vlgutv22/claude_mate/assets/photos/IMG_4897.jpg

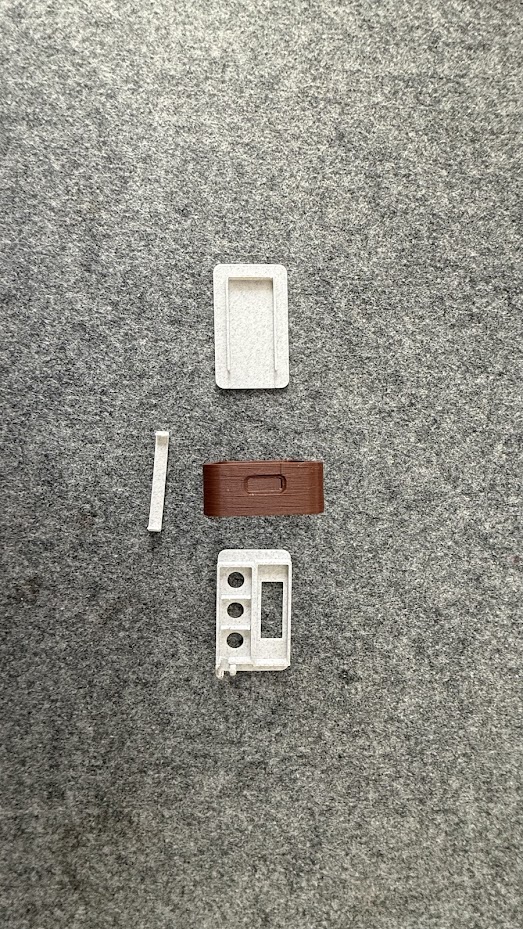
assets/photos/IMG_4897.jpg
