vlgutv22/claude_mate/assets/photos/IMG_4898.jpg

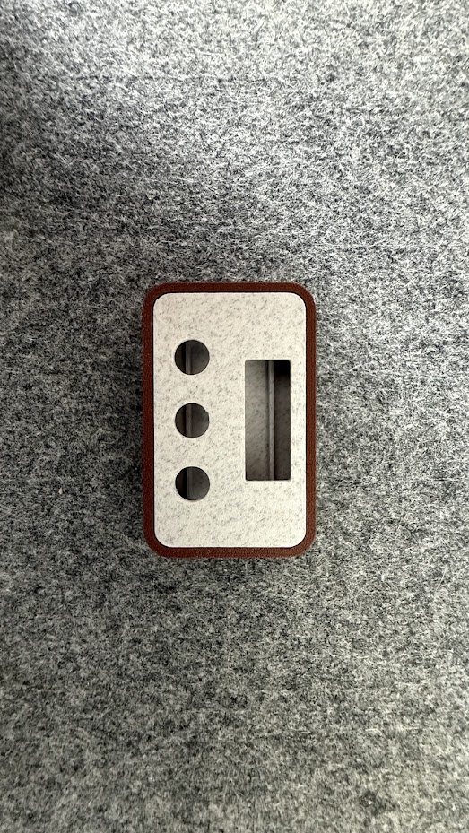
assets/photos/IMG_4898.jpg
