vlgutv22/claude_mate/assets/photos/IMG_4899.jpg

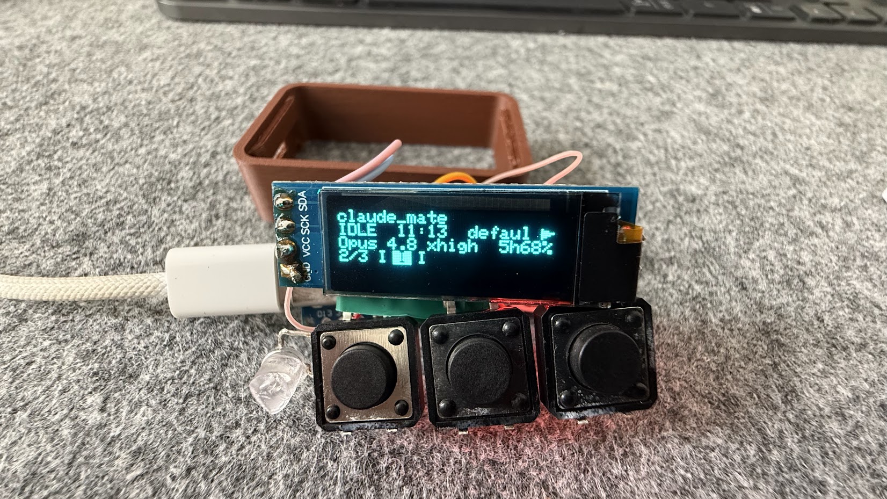
assets/photos/IMG_4899.jpg
