vlgutv22/claude_mate/assets/photos/IMG_4901.jpg

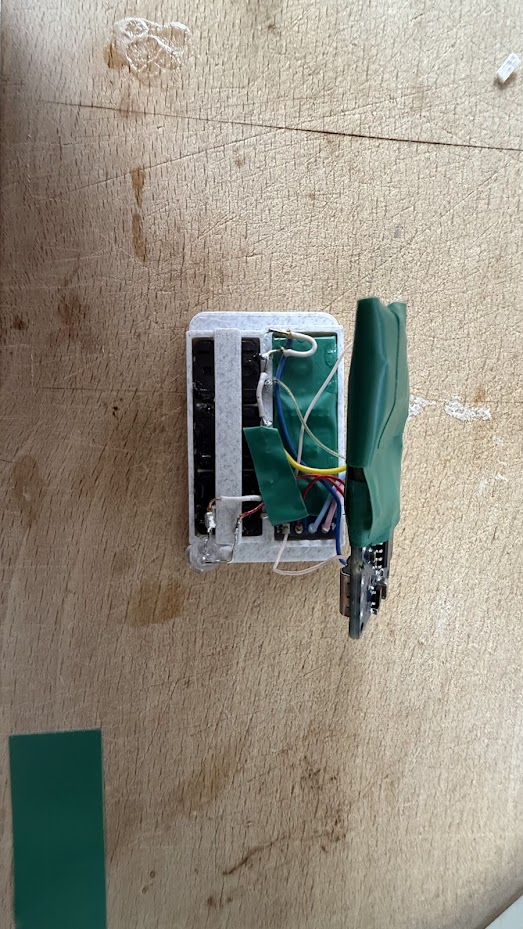
assets/photos/IMG_4901.jpg
