vlgutv22/claude_mate/assets/photos/IMG_4902.jpg

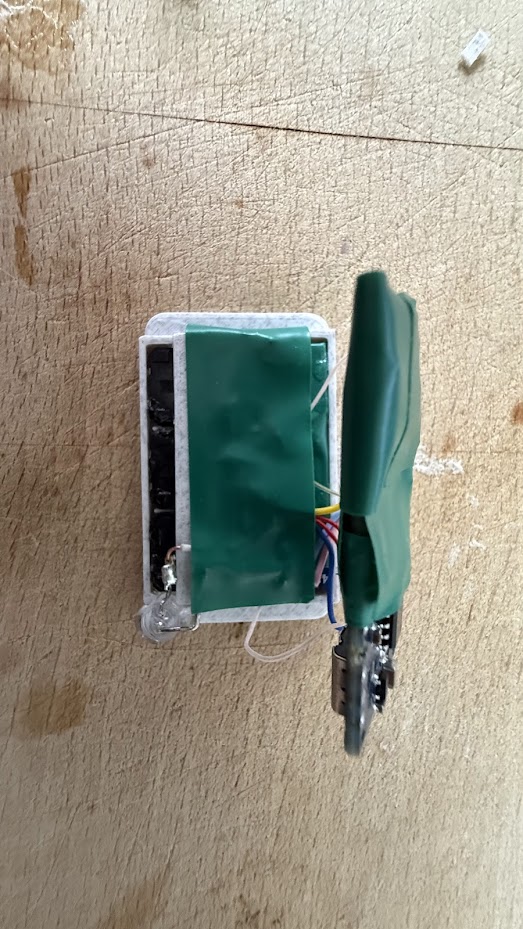
assets/photos/IMG_4902.jpg
