vlgutv22/claude_mate/assets/photos/IMG_4903.jpg

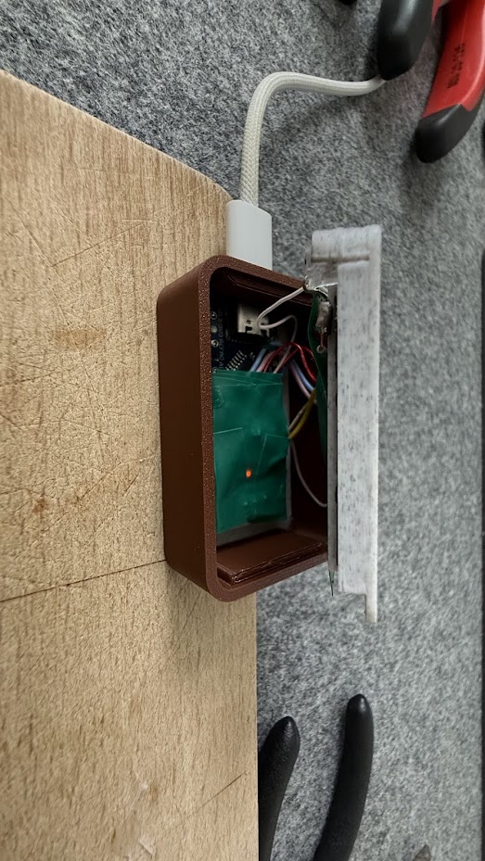
assets/photos/IMG_4903.jpg
