vlgutv22/claude_mate/assets/photos/IMG_4904.jpg

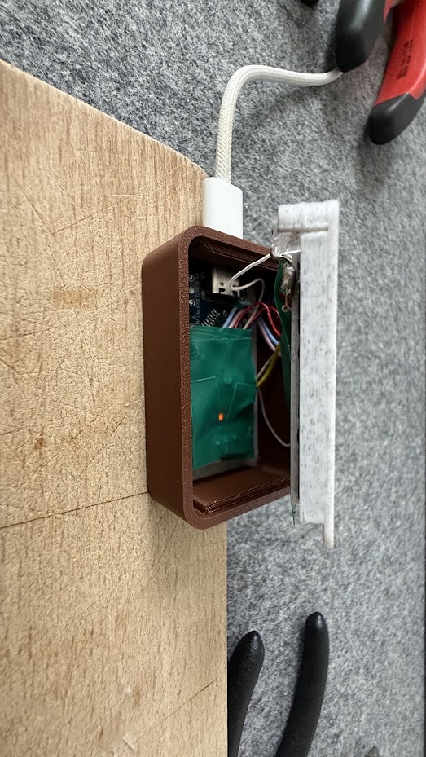
assets/photos/IMG_4904.jpg
