vlgutv22/claude_mate/assets/photos/IMG_4906.jpg

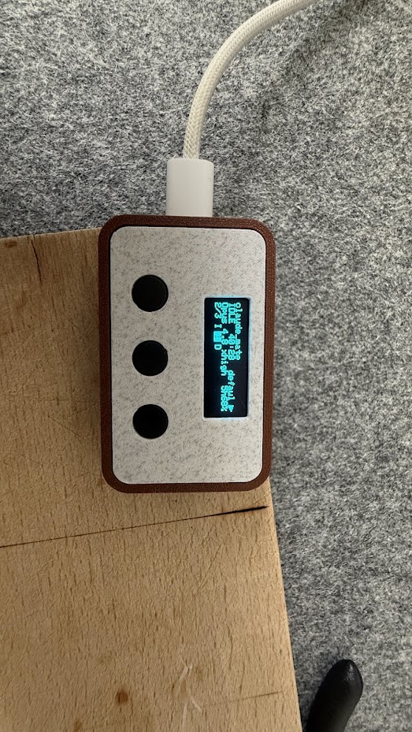
assets/photos/IMG_4906.jpg
