vlgutv22/claude_mate/assets/photos/IMG_4908.jpg

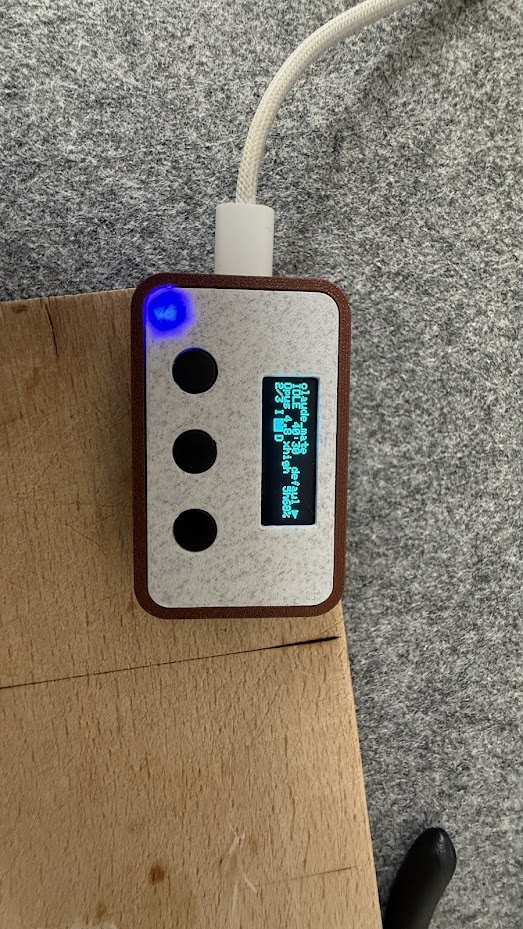
assets/photos/IMG_4908.jpg
