vlgutv22/claude_mate/assets/photos/IMG_4912.jpg

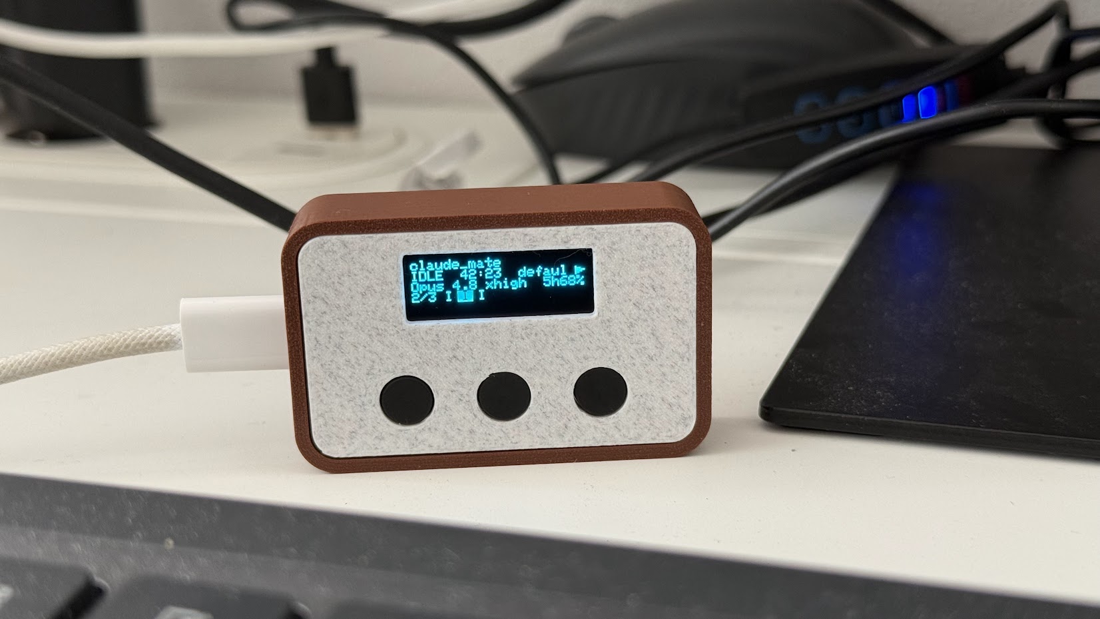
assets/photos/IMG_4912.jpg
