vlgutv22/claude_mate/daemon/claude_mate_daemon.py

#!/usr/bin/env python3
"""
Claude Mate daemon
==================

The "brain" of the Claude Mate USB hardware companion. It:

  1. Listens on a Unix-domain socket (CLAUDE_MATE_SOCK) for status lines emitted
     by Claude Code hooks / the PTY wrapper: "<state>|<session_id>|<name>[|...]".
  2. Manages the device link(s). By default that is a single, continuously-open
     USB serial connection to the Arduino Nano: it auto-detects the port
     (/dev/cu.usbserial* then /dev/cu.usbmodem*), opens it once, keeps it open,
     and auto-reconnects if it disappears. With --tcp it ALSO serves the exact
     same line protocol over TCP, so a wireless companion (the ESP32-S3 build)
     can drive the fleet from across the room. Frames fan out to every connected
     device; button events from any of them are merged into one stream, so a USB
     Nano and a WiFi device can be used side by side.
  3. Keeps ONE urgency-sorted triage queue of sessions
     (error > waiting > done > working > idle; unacknowledged before
     acknowledged inside a class; oldest event first) and renders ONE screen --
     the selected session (normally the queue head, i.e. the thing that needs
     the human most) as a pre-composed 4-row (all size-1) text frame:

         F|<flags>|<sel>|<name>|<state+time · account>|<model+effort · limit>
          |<pos + fleet letters>

     (account = which login the session runs as, limit = its remaining-limit
     chip, both right-aligned; empty for hook-driven sessions.) The firmware
     is a dumb renderer; ALL layout/ordering/selection lives here.
  4. Reads button events from the Arduino on a background thread. The buttons
     mean the same thing at all times (no modes):
        H     -> handshake; the daemon resends the full current state.
        B|P   -> PREV: selection one step up the queue (auto-repeats on hold).
        B|N   -> NEXT: selection one step down the queue (auto-repeats on hold).
        B|G   -> GO (short press): RAISE the terminal of the session SHOWN on
                 the glass (WYSIWYG -- always the name the user is looking at).
                 Raise/activate ONLY; the daemon never collapses, resizes, or
                 miniaturizes any window. An alert is acknowledged as it is
                 raised.
        B|K   -> GO (long press): acknowledge the shown session's alert WITHOUT
                 touching any window.
     A GO/ACK never auto-switches tabs -- it stays on the session it acted on.
     Double-clicking GO toggles FOLLOW mode: PREV/NEXT then also raise the
     selected terminal (raise only, after the selection settles).
  5. Drives the indication LED via V|<KIND>: the pattern for the WORST
     unacknowledged alert class, looping until acknowledged (V|OFF).

Screen ownership rule: the display NEVER changes subject on its own -- only
PREV/NEXT/GO move it. Alerts on other tabs signal through the LED and their
blinking fleet letters; the view stays where the user left it. A GO/ACK acts
on EXACTLY the session whose frame is on the glass -- never a freshly
recomputed head -- so a press can only ever raise the terminal the user is
actually looking at.

Only third-party dependency: pyserial.

Run:
    python3 daemon/claude_mate_daemon.py            # real hardware + hooks
    python3 daemon/claude_mate_daemon.py --mock     # demo with fake sessions

Config via environment variables:
    CLAUDE_MATE_PORT   serial device (default: autodetect)
    CLAUDE_MATE_SOCK   socket path   (default: /tmp/claude-mate.sock)
    CLAUDE_MATE_BAUD   serial baud   (default: 115200)
    CLAUDE_MATE_TCP    set to 1 to also serve the protocol over TCP
    CLAUDE_MATE_TCP_PORT / _TCP_BIND   listener port / bind address
    CLAUDE_MATE_TOKEN / _TOKEN_FILE    shared secret for TCP devices (required
                       for --tcp; the token itself never crosses the wire, see
                       the NetLink handshake)
"""

from __future__ import annotations

import argparse
import glob
import hmac
import json
import os
import queue
import secrets
import signal
import socket
import struct
import subprocess
import sys
import threading
import time
import traceback
import urllib.parse
import wave
from dataclasses import dataclass, field
from typing import Any, Callable, Dict, List, Optional, Tuple, Union

# --------------------------------------------------------------------------- #
# Crash-loop damage control -- BEFORE the first import that can fail
# --------------------------------------------------------------------------- #
# THIS RUNS FIRST ON PURPOSE. launchd opens our stderr (StandardErrorPath) and
# restarts us forever (KeepAlive), so a daemon that dies during import writes
# the same traceback every ThrottleInterval seconds with nothing to stop it. One
# machine reached 1786 restarts and a 50 MB log that way. A cap placed after the
# imports would never have run: the crash was `import serial` itself.
#
# TRUNCATE, DO NOT RENAME. launchd holds the fd, so renaming the file just means
# we keep writing to the same inode under its new name and the visible log stays
# empty forever. ftruncate on the fd we were handed is the only thing that works,
# and with O_APPEND the next write restarts at zero.
LOG_MAX_BYTES = int(os.environ.get("CLAUDE_MATE_LOG_MAX", 8 * 1024 * 1024))


def _cap_crash_log() -> None:
    """Keep a crash loop from eating the disk. Best effort, never fatal."""
    if LOG_MAX_BYTES <= 0:                      # opt out with CLAUDE_MATE_LOG_MAX=0
        return
    try:
        import stat
        st = os.fstat(2)
        if not stat.S_ISREG(st.st_mode) or st.st_size <= LOG_MAX_BYTES:
            return
        os.ftruncate(2, 0)
        os.lseek(2, 0, os.SEEK_SET)
        sys.stderr.write(
            f"[claude-mate] log passed {LOG_MAX_BYTES} bytes and was truncated. "
            f"If this keeps happening the daemon is crash-looping -- the error "
            f"is whatever follows this line.\n"
        )
    except Exception:                           # a pipe, a closed fd, a tty: fine
        pass


_cap_crash_log()

try:
    import serial  # pyserial
except ImportError:  # pragma: no cover - friendly error if dependency missing
    # NAME THE INTERPRETER. The failure this message used to produce was
    # "pyserial is not installed" on a machine where pyserial *was* installed --
    # in the site-packages of the Python the LaunchAgent no longer runs, because
    # /usr/local/bin/python3 is a floating symlink that a python.org update
    # repointed at a fresh version. Without sys.executable in the message there
    # is nothing to tell those two situations apart.
    sys.stderr.write(
        "[claude-mate] ERROR: pyserial is not installed for this interpreter.\n"
        f"[claude-mate]   interpreter: {sys.executable}\n"
        f"[claude-mate]   fix:         {sys.executable} -m pip install -r "
        "daemon/requirements.txt\n"
        "[claude-mate] If you installed it before and it worked, a Python "
        "upgrade probably\n"
        "[claude-mate] moved the interpreter out from under the LaunchAgent. "
        "Re-run install/install.sh,\n"
        "[claude-mate] which pins the daemon to a virtualenv it owns.\n"
    )
    raise

# --------------------------------------------------------------------------- #
# Configuration / constants
# --------------------------------------------------------------------------- #

# Primary FOCUS deep link (hook-driven VS Code sessions). See focus_session().
FOCUS_URI_TEMPLATE = "vscode://anthropic.claude-code/open?session={session_id}"

# Default config (overridable via environment).
DEFAULT_SOCK = "/tmp/claude-mate.sock"
DEFAULT_BAUD = 115200

# Serial port autodetect order (globs).
PORT_GLOBS = ("/dev/cu.usbserial*", "/dev/cu.usbmodem*")

# --- Wireless (TCP) transport ---------------------------------------------- #
# Opt-in (--tcp / CLAUDE_MATE_TCP=1). The device dials US: the daemon's address
# is stable, a DHCP device's is not.
DEFAULT_TCP_PORT = 8787
DEFAULT_TCP_BIND = "0.0.0.0"    # a remote device needs a routable address; the
                                # listener is token-gated (see NetLink)
DEFAULT_TOKEN_FILE = "~/.config/claude-mate/token"
NET_AUTH_TIMEOUT_S = 5.0    # a client must finish the handshake this fast
NET_MAX_LINE = 512          # drop over-long lines (the longest real one is ~94B)
NET_MAX_CLIENTS = 4         # bound the fan-out (a Nano + a few wireless devices)
# ...and bound the peers that have NOT authenticated yet, which is the number an
# attacker controls. Generous next to one real device, trivial next to the
# thousands a laptop can open, and every slot is released within
# NET_AUTH_TIMEOUT_S whatever the peer does or does not send.
NET_MAX_PENDING = 8
MDNS_SERVICE = "_claudemate._tcp"   # advertised via macOS dns-sd so the device
# --- Which networks the listener is allowed to exist on -------------------- #
# THE LISTENER USED TO BE UNCONDITIONAL, and its own docstring explained why
# that was only ever half a design: "the payload itself is plaintext... use it
# on a network you trust". It said nothing about what happens when you carry the
# Mac somewhere else, and the answer was that port 8787 opened itself to a cafe
# exactly as readily as to your living room, and dns-sd announced it to everyone
# on the segment while it did.
#
# A NETWORK IS IDENTIFIED BY ITS GATEWAY'S MAC ADDRESS. Not by SSID: modern
# macOS redacts the SSID and BSSID from every API a daemon can reach without
# Location Services permission, which a LaunchAgent cannot raise a prompt for.
# Not by subnet either -- half the cafes in the world are 192.168.1.0/24, and so
# is half of everyone's house. The gateway's MAC is available from the routing
# table plus the ARP cache, needs no permission, no sudo and no dependency, and
# it actually distinguishes your router from a stranger's.
#
# BE HONEST ABOUT WHAT THIS IS. It is a strong practical control and NOT a
# cryptographic one: someone already on your LAN who knows your home gateway's
# MAC could forge it. It stops the daemon from offering itself to networks you
# have never seen; it does not turn a hostile LAN into a safe one. The plaintext
# threat model above still applies on any network you do trust.
TRUSTED_FILE = "~/.config/claude-mate/trusted-networks"
NET_GATE_POLL_S = 20.0      # how often to re-check which network we are on

MDNS_NAME = "Claude Mate"           # finds the daemon with zero configuration

# Timings (seconds).
DOUBLE_CLICK_S = 0.30        # two GO short-presses within this window = a
                             # double-click (toggles FOLLOW mode). A single GO
                             # is deferred this long to disambiguate.
# ---- MIRROR (the device's terminal view) ---------------------------------- #
# The colour screen fits 53x21 characters at size 1; the status bar takes the
# top band, leaving MIRROR_ROWS for content. Claude's TUI is 80-120 columns
# wide, so rows are CLIPPED, not reflowed -- wrapping a TUI whose box drawing
# and alignment carry meaning turns it into noise, and a clipped-but-truthful
# view is easier to read than a rewrapped one.
MIRROR_COLS = 52
MIRROR_ROWS = 17
MIRROR_POLL_S = 1.0          # refresh cadence while the view is open; polling
                             # stops entirely when it is closed, so an unwatched
                             # fleet costs nothing

FOLLOW_SETTLE_S = 0.25       # in FOLLOW mode, PREV/NEXT raise the selected
                             # terminal only after the selection settles this
                             # long -- so holding to scroll doesn't raise every
                             # window it passes over (raise ONLY, never collapse)
REALERT_SUPPRESS_S = 5.0     # a session re-entering the SAME alert class this
                             # soon after being acknowledged stays acknowledged
                             # (absorbs detection flaps re-firing the LED)
WRAPPER_LIVE_TIMEOUT_S = 1.0  # a live wrapper acks receipt ('go') within ms; a
                              # wedged one (stopped process: the kernel accepts
                              # the connect into the backlog and buffers the
                              # send) costs only this per focus, not the
                              # full completion deadline
WRAPPER_ACK_TIMEOUT_S = 12.0  # overall deadline for the completion ack ('ok');
                              # must exceed the wrapper's worst-case focus op
                              # (~10s: tmux select-window/pane + osascript).
                              # Pre-ack wrappers close the socket at once (EOF),
                              # so the wait degrades to fire-and-forget.
NOTICE_S = 4.0              # how long a transient message holds the middle two
                            # rows. Long enough to read at arm's length after
                            # looking down at the press, short enough that the
                            # screen is never lying about a session for long.
PING_PERIOD = 15.0          # keepalive ping interval
RECONNECT_DELAY = 2.0       # wait between serial (re)connection attempts
SESSION_DONE_TTL = 120.0    # drop a 'done' session after this long with no update
SESSION_IDLE_TTL = 600.0    # drop any stale session after this long

# Screen text geometry (must match the firmware's fixed 4-row layout, all
# size-1: r0 name / r1 state+time / r2 model+effort / r3 position + fleet).
ROW_CHARS = 21              # size-1 rows are 21 chars wide (128 / 6px)

# 4-char state tag shown on the state row.
STATE_TAG = {"working": "WORK", "waiting": "WAIT", "error": "ERR",
             "done": "DONE", "idle": "IDLE"}

# One LETTER per session in the fleet strip (queue order), '|'-separated:
#   I idle  E error  W working (WIP)  D done  B waiting (blocked, needs input)
STATE_LETTER = {"error": "E", "waiting": "B", "working": "W",
                "done": "D", "idle": "I"}

# Triage priority, most urgent first. The queue sorts by
# (class rank, acknowledged?, event time): a fresh error outranks everything,
# unacknowledged before acknowledged inside a class, oldest first (FIFO triage).
STATE_ORDER = {"error": 0, "waiting": 1, "done": 2, "working": 3, "idle": 4}

VALID_STATES = set(STATE_ORDER.keys())

# Alert states nag the human until acknowledged (GO/ACK) or the state changes.
ALERT_STATES = {"error", "waiting", "done"}

# One-shot LED kind on a fresh transition INTO each alert state.
ALERT_KIND = {"error": "ERROR", "waiting": "INPUT", "done": "DONE"}

# Every "until acknowledged" alert plays as a CONTINUOUS firmware LED loop with
# its own distinct rhythm. The firmware repeats the pattern until V|OFF (sent
# when the last unacknowledged member of the class is acknowledged/cleared).
LOOP_KIND = {"error": "ERROR", "waiting": "INPUT", "done": "DONE"}

# ---- Alert sounds (macOS, opt-in) ------------------------------------------ #
# The device itself cannot make a sound: the ESP32-S3 has no DAC, and the
# Waveshare board's 3.3 V rail is a linear LDO with the backlight on a plain
# resistor-limited MOSFET -- there is no switching node whose current the
# firmware could modulate into anything audible. So until a piezo is soldered
# on, the Mac is the only speaker in the system.
#
# That is not purely a workaround. When you are AT the Mac it is the better
# channel: real speakers, distinguishable sounds, and it follows the system
# volume. It stops being enough exactly when the device is across the room on
# battery -- which is the case the piezo will eventually cover.
#
# Off by default. An audible alert on every state change is far more intrusive
# than a colour change, and that has to be opted into rather than inherited.
SOUND_DIR = "/System/Library/Sounds"
ALERT_SOUNDS = {
    "ERROR": "Basso.aiff",     # descending, unmistakably "something went wrong"
    "INPUT": "Glass.aiff",     # bright and short: a question, not a failure
    "DONE":  "Hero.aiff",      # rising, resolved
    "START": "Pop.aiff",       # a tick; only fires when nothing else is pending
}
SOUND_MIN_GAP_S = 2.0          # floor between sounds, whatever the state does

# SHIP IT, the game on the device, over `O|SFX|<code>`. The board has no DAC, no
# speaker and a backlight circuit with no inductor to abuse, so if the game is to
# make a noise at all it has to be this machine making it.
#
# These were macOS system alert sounds for one version, and that was wrong in a
# way that only shows up when you play: Basso and Glass are the vocabulary of an
# OS telling you something, not of a game. The browser prototype uses WebAudio
# square and sawtooth oscillators, and THAT is the sound the device should make
# -- so the recipes below are the prototype's literals, and the daemon renders
# them to WAV once at startup rather than reaching for a file someone at Apple
# designed for a different purpose.
#
#   (frequencies Hz), note seconds, waveform, peak gain
#
# A recipe of several frequencies is played as a SEQUENCE, one note per entry,
# each `dur` long -- that is what makes the merge an arpeggio and the ship a
# fanfare rather than a chord.
SFX_RECIPES = {
    "J": ((520, 760),                  0.055, "square",   0.050),  # jump
    "S": ((300, 150),                  0.050, "square",   0.050),  # stomped a bug
    "M": ((660, 880, 1320),            0.065, "square",   0.055),  # merged a PR
    "H": ((180, 120),                  0.090, "sawtooth", 0.050),  # a bug got you
    "R": ((180, 120),                  0.090, "sawtooth", 0.050),  # re-scoped
    "F": ((400, 260, 160),             0.060, "sawtooth", 0.050),  # fell
    "X": ((400, 260, 160),             0.060, "sawtooth", 0.050),  # slipped
    "W": ((523, 659, 784, 1047, 1319), 0.110, "square",   0.060),  # shipped
}
# R and X are not distinct sounds, and that is the prototype's choice rather
# than an oversight here: a priority change reads as a hit and a slipped
# milestone reads as a fall, which is what they are.

# The prototype's gains are WebAudio linear gain into a browser, and the same
# numbers rendered to a file and pushed through afplay land far below the system
# alerts they sit beside -- quiet enough to miss over a fan. Everything is scaled
# by this one factor, so the sounds keep their RELATIVE levels (the ship fanfare
# stays the loudest) while landing somewhere a person can hear.
SFX_GAIN     = 5.0
SFX_RATE     = 44100
SFX_ATTACK_S = 0.008           # the prototype's linear attack, then exp decay
SFX_FLOOR    = 0.0008          # ...to here, which is where its ramp ends

# Rendered WAVs live here. The version in the name is load-bearing: change a
# recipe without changing it and every machine keeps playing the old sound from
# cache forever.
SFX_CACHE_DIR = os.path.join(
    os.path.expanduser("~/Library/Caches/claude-mate"), "sfx-v1")

GAME_SOUND_MIN_GAP_S = 0.06

# A device with no token redials every couple of seconds; say what to do about
# it at most this often, or the advice buries itself.
NO_TOKEN_LOG_GAP_S = 60.0

# Sentinel for "we have not told the firmware a loop state yet", so the first
# resolve always emits (V|OFF) and clears any stale loop left by a prior daemon.
_LOOP_UNSET = "\x00unset"


def _sfx_render(freqs, dur: float, wave: str, vol: float) -> bytes:
    """One recipe -> 16-bit mono PCM, reproducing WebAudio's envelope exactly.

    The prototype gives each note its own oscillator and gain node, ramps the
    gain linearly 0 -> vol over 8 ms, then EXPONENTIALLY down to 0.0008 by the
    note's end. The exponential matters: a linear fade of a square wave at these
    durations sounds like a click with a tail, and the whole character of the
    thing is in that decay curve. WebAudio's exponentialRampToValueAtTime is
    v0 * (v1/v0)^(progress), which is what the pow() below is.

    Naive (non-band-limited) square and sawtooth, deliberately. WebAudio uses
    band-limited wavetables, so this aliases slightly where that does not -- at
    these frequencies the difference is inaudible, and the alternative is a
    Fourier synthesis nobody can check against the prototype by ear."""
    frames = bytearray()
    span   = max(dur - SFX_ATTACK_S, 1e-6)
    ratio  = SFX_FLOOR / vol
    peak   = min(vol * SFX_GAIN, 0.85)         # headroom against clipping
    for f in freqs:
        n = int(SFX_RATE * dur)
        for i in range(n):
            t = i / SFX_RATE
            if t < SFX_ATTACK_S:
                env = t / SFX_ATTACK_S
            else:
                env = pow(ratio, (t - SFX_ATTACK_S) / span)
            # Phase restarts per note, as it must: the prototype creates a new
            # oscillator for each one.
            ph = (f * t) % 1.0
            sample = (2.0 * ph - 1.0) if wave == "sawtooth" else (1.0 if ph < 0.5 else -1.0)
            v = int(max(-1.0, min(1.0, peak * env * sample)) * 32767)
            frames += struct.pack("<h", v)
    return bytes(frames)


def sfx_build_cache() -> dict:
    """Render every recipe to a WAV once and return {code: path}.

    Returns {} on any failure -- a game with no sound is a working game, and a
    daemon that will not start because it could not write a beep is not."""
    out = {}
    try:
        os.makedirs(SFX_CACHE_DIR, exist_ok=True)
        for code, (freqs, dur, wave_t, vol) in SFX_RECIPES.items():
            path = os.path.join(SFX_CACHE_DIR, f"{code}.wav")
            if not os.path.exists(path):
                pcm = _sfx_render(freqs, dur, wave_t, vol)
                # Written to a temp name and renamed, so a daemon killed
                # mid-render cannot leave a truncated WAV cached forever.
                tmp = path + ".part"
                with wave.open(tmp, "wb") as w:
                    w.setnchannels(1)
                    w.setsampwidth(2)
                    w.setframerate(SFX_RATE)
                    w.writeframes(pcm)
                os.replace(tmp, path)
            out[code] = path
    except Exception as exc:
        log(f"game sound: could not build the cache ({exc}); game is silent")
        return {}
    return out


def log(msg: str) -> None:
    """Clean, timestamped logging to stderr."""
    ts = time.strftime("%H:%M:%S")
    sys.stderr.write(f"[claude-mate {ts}] {msg}\n")
    sys.stderr.flush()


# --------------------------------------------------------------------------- #
# Session model + thread-safe registry
# --------------------------------------------------------------------------- #


@dataclass
class Session:
    """One Claude Code session tracked by the daemon."""
    key: str                       # registry key (session_id or name)
    name: str                      # cwd basename, display name
    state: str = "idle"            # working | waiting | error | done | idle
    sid: str = ""                  # session_id (may be empty)
    cwd: str = ""                  # working directory, if known
    last_update_ts: float = field(default_factory=time.time)
    state_since: float = field(default_factory=time.time)  # when current state began
    model: str = ""                # model in use, e.g. "Opus 4.8" (PTY wrapper)
    effort: str = ""               # effort level, e.g. "xhigh" (PTY wrapper)
    account: str = ""              # account the session runs as, e.g. "work" (PTY wrapper)
    limit: str = ""                # remaining-limit chip, e.g. "5h82%" (PTY wrapper)
    focus_ctrl: str = ""           # PTY-wrapper control socket for FOCUS (if any)
    acked: bool = True             # alert (done/waiting/error) seen by the human?
    last_ack_state: str = ""       # alert class most recently acknowledged...
    last_ack_ts: float = 0.0       # ...and when (re-alert flap suppression)

    def display_seconds(self) -> float:
        """The time shown on the info row: time in the current state.

        For 'working' that IS the live turn runtime; for an alert state it is
        the triage-critical number -- how long this has been waiting on the
        human; for 'idle' how long it has been sitting there.
        """
        return max(0.0, time.time() - self.state_since)

    def unacked_alert(self) -> bool:
        return self.state in ALERT_STATES and not self.acked


class Registry:
    """Thread-safe collection of sessions keyed by session_id (or name)."""

    def __init__(self) -> None:
        self._lock = threading.Lock()
        self._sessions: Dict[str, Session] = {}

    def update(self, state: str, sid: str, name: str, cwd: str = "",
               focus_ctrl: str = "", model: str = "",
               effort: str = "", account: str = "",
               limit: str = "") -> Optional[str]:
        """Apply a status update from a hook, the PTY wrapper, or the mock injector.

        Returns the one-shot LED KIND for this session's own transition
        (START/DONE/INPUT/ERROR), or None for a keepalive / silent change.

        Models "finished but not yet acknowledged": a turn ending (working ->
        idle) becomes 'done' and STAYS 'done' (alerting) until the user
        acknowledges it; later idle keepalives must not clear it.
        """
        if state not in VALID_STATES:
            log(f"ignoring update with invalid state: {state!r}")
            return None
        key = sid if sid else (name if name else "unknown")
        now = time.time()
        with self._lock:
            sess = self._sessions.get(key)
            if sess is None:
                sess = Session(key=key, name=name or key)
                self._sessions[key] = sess
            # Update fields.
            if name:
                sess.name = name
            if sid:
                sess.sid = sid
            if cwd:
                sess.cwd = cwd
            if focus_ctrl:
                sess.focus_ctrl = focus_ctrl
            if model:
                sess.model = model
            if effort:
                sess.effort = effort
            if account:
                sess.account = account
            if limit:
                sess.limit = limit
            prev_state = sess.state
            sess.last_update_ts = now

            # Resolve the EFFECTIVE state under the done-until-acknowledged model.
            eff = state
            if state == "idle":
                if prev_state == "working":
                    eff = "done"                 # just finished -> needs ack
                elif prev_state == "done" and not sess.acked:
                    eff = "done"                 # keepalive while unacknowledged

            changed = (eff != prev_state)
            if changed:
                sess.state_since = now           # live "time in state" anchor
            sess.state = eff

            # Acknowledgment + one-shot LED kind on a real transition.
            haptic: Optional[str] = None
            if changed:
                if eff in ALERT_STATES:          # done/waiting/error: fresh alert
                    # Flap suppression: re-entering the SAME alert class right
                    # after the human acknowledged it stays acknowledged, so a
                    # bouncing detector can't re-fire the LED he just silenced.
                    if (sess.last_ack_state == eff
                            and (now - sess.last_ack_ts) < REALERT_SUPPRESS_S):
                        sess.acked = True
                    else:
                        sess.acked = False       # nag until acknowledged
                        haptic = ALERT_KIND[eff]
                elif eff == "working":
                    sess.acked = True
                    sess.last_ack_state = ""     # real forward progress: a
                    sess.last_ack_ts = 0.0       # future alert is NEW, not a flap
                    haptic = "START"             # job (re)started: calm tick
                else:                            # idle
                    sess.acked = True
            return haptic

    def remove(self, key: str) -> None:
        with self._lock:
            self._sessions.pop(key, None)

    def acknowledge(self, sess: Optional["Session"]) -> None:
        """GO/ACK pressed: mark this session's alert as seen. A finished (done)
        session becomes idle; a waiting/error session is silenced but keeps its
        state (it still shows, just stops nagging) until it changes on its own."""
        if sess is None:
            return
        with self._lock:
            if sess.state in ALERT_STATES:
                sess.last_ack_state = sess.state
                sess.last_ack_ts = time.time()
            sess.acked = True
            if sess.state == "done":
                sess.state = "idle"
                sess.state_since = time.time()

    def top_alert(self) -> Optional["Session"]:
        """The most urgent unacknowledged session needing the human (error >
        waiting > done, oldest first), or None. Drives the LED loop class.
        Sorted by URGENCY independently of the display order (which is a
        stable alphabetical order, see queue())."""
        with self._lock:
            items = [s for s in self._sessions.values() if s.unacked_alert()]
        items.sort(key=lambda s: (STATE_ORDER.get(s.state, 99), s.state_since))
        return items[0] if items else None

    def prune(self) -> None:
        """Drop stale/finished sessions so the queue stays tidy."""
        now = time.time()
        with self._lock:
            dead: List[str] = []
            for key, s in self._sessions.items():
                age = now - s.last_update_ts
                if s.state == "idle" and age > SESSION_IDLE_TTL:
                    dead.append(key)
                elif s.state == "done" and age > SESSION_DONE_TTL:
                    dead.append(key)
                elif age > SESSION_IDLE_TTL:
                    dead.append(key)
            for key in dead:
                self._sessions.pop(key, None)
            if dead:
                log(f"pruned {len(dead)} stale session(s)")

    def queue(self) -> List[Session]:
        """The display/navigation order: STABLE, alphabetical by name (then key
        as a deterministic tiebreak). Tabs keep their position as their states
        change -- they never shuffle under the user. Urgency drives the LED
        separately (see top_alert()), not this order."""
        with self._lock:
            items = list(self._sessions.values())
        items.sort(key=lambda s: (s.name.lower(), s.key))
        return items

    def count(self) -> int:
        with self._lock:
            return len(self._sessions)


# --------------------------------------------------------------------------- #
# Serial link: open once, keep open, auto-reconnect.
# --------------------------------------------------------------------------- #


class SerialLink:
    """Owns the single serial connection and serializes writes."""

    def __init__(self, port: Optional[str], baud: int) -> None:
        self._configured_port = port  # None => autodetect
        self._baud = baud
        self._ser: Optional[serial.Serial] = None
        self._lock = threading.Lock()  # guards writes + (re)connect
        self._provision_token: Optional[str] = None
        self._pending_provision = False   # armed on open, spent on the first K/H

    def set_provision_token(self, token: Optional[str]) -> None:
        """The secret to hand a device that arrives on the cable. See _provision().

        Set only when a wireless transport is up, because that is the only time
        there is a shared secret to share -- a USB-only daemon has nothing to
        provision the device FOR.
        """
        self._provision_token = token

    @staticmethod
    def autodetect() -> Optional[str]:
        """Find a likely Arduino device by glob priority."""
        for pattern in PORT_GLOBS:
            matches = sorted(glob.glob(pattern))
            if matches:
                return matches[0]
        return None

    def _resolve_port(self) -> Optional[str]:
        if self._configured_port:
            return self._configured_port if os.path.exists(self._configured_port) else None
        return self.autodetect()

    def is_open(self) -> bool:
        return self._ser is not None and self._ser.is_open

    # Same names LinkHub exposes, so the maintainer can drive either link type
    # without caring which transport it got.
    def serial_is_open(self) -> bool:
        return self.is_open()

    def ensure_serial_open(self) -> bool:
        return self.ensure_open()

    def ensure_open(self) -> bool:
        """Try to (re)open the port. Returns True if open afterwards."""
        with self._lock:
            if self.is_open():
                return True
            port = self._resolve_port()
            if not port:
                return False
            try:
                self._ser = serial.Serial(
                    port=port,
                    baudrate=self._baud,
                    bytesize=serial.EIGHTBITS,
                    parity=serial.PARITY_NONE,
                    stopbits=serial.STOPBITS_ONE,
                    timeout=0.5,        # read timeout
                    write_timeout=2.0,
                )
                log(f"serial opened on {port} @ {self._baud} 8N1")
                # Opening the port resets the Nano (~1.5s); it will emit H when
                # ready, prompting a full state resend. We do not block here.
                #
                # The token is NOT sent yet -- see provision_if_ours(). A `P`
                # asks whoever is on this port to identify itself; a Claude Mate
                # answers `K` (or `H` on boot), and only then does a secret go
                # down the wire.
                self._pending_provision = True
                self._write_locked("P")
                return True
            except (serial.SerialException, OSError) as exc:
                log(f"serial open failed on {port}: {exc}")
                self._close_locked()
                return False

    def provision_if_ours(self) -> None:
        """The device answered the protocol, so it is safe to give it the token.

        Called by the reader when a `K` or `H` arrives. THE HANDSHAKE IS THE
        POINT: autodetect() takes the first match of a glob, and PORT_GLOBS tries
        `/dev/cu.usbserial*` BEFORE the `/dev/cu.usbmodem*` the S3 actually
        enumerates as -- so any FTDI or CH340 dongle on the desk outranked the
        real device and was handed the shared secret, on every reconnect. It
        cannot answer `K`, so it no longer gets one.
        """
        with self._lock:
            if not self._pending_provision:
                return
            self._pending_provision = False
            self._provision_locked()

    def _write_locked(self, line: str) -> None:
        """Write with the lock already held. Failures are the caller's problem."""
        if not self.is_open():
            return
        try:
            self._ser.write((line + "\n").encode("ascii", errors="replace"))
        except (serial.SerialException, OSError):
            pass

    def _provision_locked(self) -> None:
        """Give the device on the cable this daemon's token, once per open.

        THE CABLE IS THE ANSWER TO "how do I connect it after a factory reset",
        and it should not involve the human at all. A wiped board comes up on
        BLE with no token; the daemon connects, gets A|NOTOKEN, and both ends
        then sit there knowing exactly what is wrong and doing nothing about it
        -- while a USB cable, over which provisioning is already the documented
        and trusted path, is plugged into the same two devices.

        Unconditional rather than conditional on "does it need one", because
        there is no way to ask over this link (USB has no handshake -- it is
        trusted by being physical) and because the daemon's token is the
        authority: a device holding a different one is a device that cannot
        link, so overwriting is the repair, not a side effect. NVS skips a write
        whose value is unchanged, so the steady state costs nothing.

        T| is a CONFIG verb, handled before the protocol on the firmware side,
        and the Nano ignores it as an unknown line -- so this is safe to send to
        whatever happens to be on the port.
        """
        token = self._provision_token
        if not token or os.environ.get("CLAUDE_MATE_NO_USB_PROVISION") == "1":
            return
        # THE PORT CAN CLOSE BETWEEN THE ARM AND THE WRITE, and it is not a rare
        # window: the arm is spent by a K/H reaching the ButtonReader, which the
        # hub forwards here from WHATEVER transport it arrived on -- so a device
        # that drops off the cable and says hello over the radio a few seconds
        # later lands exactly here with `self._ser` already None. That is an
        # AttributeError, not a SerialException, so the except below did not
        # catch it and it killed the reader thread. Observed in the wild: a
        # serial read failure at 21:37:42 and a BLE connect at 21:37:48 left the
        # daemon running with every device button dead.
        if not self.is_open():
            return
        try:
            self._ser.write(f"T|{token}\n".encode("ascii", errors="replace"))
        except (serial.SerialException, OSError) as exc:
            # Not fatal and not worth closing the port over: the link still
            # works, it just may not be able to authenticate over the radio.
            log(f"serial: could not hand the device a token: {exc}")
            return
        log("serial: handed the device this daemon's token (USB provisioning)")

    def _close_locked(self) -> None:
        if self._ser is not None:
            try:
                self._ser.close()
            except Exception:
                pass
        self._ser = None
        # The arm belongs to the open that made it. Leaving it set means the
        # next K/H -- possibly from a device that is now on the radio, with no
        # cable at all -- tries to provision a port that is gone; ensure_open()
        # re-arms it if and when the cable comes back.
        self._pending_provision = False

    def close(self) -> None:
        with self._lock:
            self._close_locked()

    def write_line(self, line: str) -> bool:
        """Write one newline-terminated ASCII line. Returns success."""
        data = (line.rstrip("\n") + "\n").encode("ascii", errors="replace")
        with self._lock:
            if not self.is_open():
                return False
            try:
                # No flush(): tcdrain has no timeout bound, and a wedged port
                # would stall every caller holding the Screen lock. write() is
                # bounded by write_timeout and these lines are tiny; the kernel
                # drains them at line rate.
                self._ser.write(data)
                return True
            except (serial.SerialException, OSError) as exc:
                log(f"serial write failed ({line!r}): {exc}")
                self._close_locked()  # mark dead -> reconnect loop will recover
                return False

    def read_line(self) -> Optional[str]:
        """Read one line (blocking up to the read timeout). None on no-data/err."""
        ser = self._ser
        if ser is None or not ser.is_open:
            return None
        try:
            raw = ser.readline()
        except (serial.SerialException, OSError) as exc:
            log(f"serial read failed: {exc}")
            self.close()
            return None
        if not raw:
            return None
        try:
            return raw.decode("ascii", errors="replace").strip()
        except Exception:
            return None


# --------------------------------------------------------------------------- #
# Wireless link: the same line protocol over TCP (opt-in).
# --------------------------------------------------------------------------- #


def load_token(explicit: Optional[str]) -> Optional[str]:
    """Resolve the shared secret: --token/env first, then the token file.

    A file keeps the secret out of the LaunchAgent plist (which is readable by
    every process on the machine); we require it to be non-empty but do not
    enforce permissions, since the user may deliberately share it.
    """
    if explicit:
        return explicit.strip() or None
    path = os.path.expanduser(os.environ.get("CLAUDE_MATE_TOKEN_FILE",
                                             DEFAULT_TOKEN_FILE))
    try:
        with open(path, "r", encoding="utf-8") as fh:
            return fh.read().strip() or None
    except OSError:
        return None


def ensure_token(explicit: Optional[str]) -> Optional[str]:
    """load_token(), but MAKE one rather than refusing if there is none.

    --tcp used to fail closed on a missing token and fall back to USB-only,
    which was the right instinct aimed at the wrong problem. The danger being
    guarded against is an UNAUTHENTICATED listener; a freshly generated 32-byte
    secret is not that. What the old behaviour actually produced was a dead end:
    the device's setup portal asks for a token, and the only way to have one was
    to have already known to create the file by hand. Generating it here closes
    that loop -- run the daemon once, read the token off the terminal, type it
    into the portal.

    Written 0600, and only ever created; an existing file is never rewritten, so
    this cannot silently invalidate a device that is already provisioned.
    """
    tok = load_token(explicit)
    if tok:
        return tok
    if explicit:                       # they passed one and it was blank
        return None
    path = os.path.expanduser(os.environ.get("CLAUDE_MATE_TOKEN_FILE",
                                             DEFAULT_TOKEN_FILE))
    tok = secrets.token_hex(32)
    try:
        os.makedirs(os.path.dirname(path), exist_ok=True)
        # Create-exclusive: if another daemon raced us to it, read theirs rather
        # than clobbering a token a device may already be provisioned with.
        fd = os.open(path, os.O_WRONLY | os.O_CREAT | os.O_EXCL, 0o600)
        with os.fdopen(fd, "w", encoding="utf-8") as fh:
            fh.write(tok + "\n")
    except FileExistsError:
        return load_token(None)
    except OSError as exc:
        log(f"ERROR: could not create a token at {path}: {exc}")
        return None
    log("")
    log("  no shared token existed, so one was generated:")
    log("")
    log(f"      {tok}")
    log("")
    log(f"  saved to {path} (mode 0600).")
    log("  Type it into the device's wifi setup portal, in 'Shared token'.")
    log("")
    return tok


class NetLink:
    """Serves the daemon<->device line protocol to token-authenticated TCP peers.

    The device is the CLIENT: the daemon's address is stable and discoverable
    (mDNS), a DHCP device's is not, and dialling out means the device needs no
    inbound reachability at all.

    HANDSHAKE (the token never crosses the wire, so sniffing one session cannot
    reveal it and a captured handshake cannot be replayed against a later one):

        daemon -> device   C|<nonce>          32 hex chars, fresh per connection
        device -> daemon   A|<mac>            hex HMAC-SHA256(token, nonce)
        daemon -> device   A|OK               ...or A|NO and the socket closes

    After A|OK the socket carries exactly the bytes the serial link would: F|/V|/P
    down, H/K/B| up. The device sends H, which makes the daemon resend full state
    -- the same recovery path a Nano replug uses.

    Writes fan out to every authenticated client and reads from all of them merge
    into one queue, so a USB Nano and a wireless device work side by side. A
    device that vanishes without a FIN (walked out of WiFi range) is reaped the
    first time a frame or ping fails to send.

    THREAT MODEL: the payload itself is plaintext. Anyone who can sniff your LAN
    can read session names, models and states, and an on-path attacker could
    inject button events into an established connection. Use it on a network you
    trust; it is off unless you ask for it.
    """

    def __init__(self, bind: str, port: int, token: str,
                 rx: "queue.Queue[str]") -> None:
        self._bind = bind
        self._port = port
        self._token = token.encode("utf-8")
        self._rx = rx
        self._srv: Optional[socket.socket] = None
        self._lock = threading.Lock()           # guards _clients
        self._clients: List[socket.socket] = []
        self._stop_evt = threading.Event()
        self._threads: List[threading.Thread] = []
        self._pending = 0                       # connections still handshaking
        self._no_token_logged = 0.0             # throttle for _log_no_token

    # ---- lifecycle -------------------------------------------------------- #

    def start(self) -> bool:
        """Bind + listen and start accepting. False if the port is unusable.

        RESTARTABLE, because NetworkGate closes the listener when the Mac moves
        to an untrusted network and opens it again when it comes home. stop()
        sets _stop_evt and nothing used to clear it, so the second start() built
        a listener and handed it to an accept loop whose very first `while not
        self._stop_evt.is_set()` was already false -- a socket bound, listening,
        and attached to nobody, which is worse than a failure because it looks
        exactly like success.
        """
        self._stop_evt.clear()
        # Drop the corpses of previous connections. This list is appended to
        # once per accepted connection and never pruned, so on a long-lived
        # daemon it is an unbounded list of dead Thread objects -- slow-motion
        # memory growth that anyone able to reach the port can drive.
        self._threads = [t for t in self._threads if t.is_alive()]
        try:
            srv = socket.socket(socket.AF_INET, socket.SOCK_STREAM)
            srv.setsockopt(socket.SOL_SOCKET, socket.SO_REUSEADDR, 1)
            srv.bind((self._bind, self._port))
            srv.listen(NET_MAX_CLIENTS)
            srv.settimeout(0.5)                 # so the accept loop can stop
        except OSError as exc:
            log(f"TCP listen failed on {self._bind}:{self._port}: {exc}")
            return False
        self._srv = srv
        t = threading.Thread(target=self._accept_loop, name="net-accept",
                             daemon=True)
        t.start()
        self._threads.append(t)
        log(f"TCP listening on {self._bind}:{self._port} (token required)")
        return True

    def stop(self) -> None:
        self._stop_evt.set()
        if self._srv is not None:
            # SHUTDOWN BEFORE CLOSE, and it is not belt-and-braces. close() on
            # a listening socket does not wake a thread already blocked in
            # accept() on Linux, and the kernel keeps the socket serving until
            # that thread lets go -- so "the listener is closed" was true of our
            # bookkeeping and false of the port for up to one accept timeout.
            # For a control whose whole job is to shut the door when the Mac
            # joins a network you do not trust, "closed in a moment" is not the
            # same promise as "closed". shutdown() wakes the accept immediately;
            # it is meaningless on a listening socket on some platforms, hence
            # the guard rather than a check.
            try:
                self._srv.shutdown(socket.SHUT_RDWR)
            except OSError:
                pass
            try:
                self._srv.close()
            except OSError:
                pass
            self._srv = None
        with self._lock:
            clients, self._clients = self._clients, []
        for c in clients:
            self._shutdown(c)

    @staticmethod
    def _shutdown(sock: socket.socket) -> None:
        try:
            sock.shutdown(socket.SHUT_RDWR)
        except OSError:
            pass
        try:
            sock.close()
        except OSError:
            pass

    # ---- accept + authenticate -------------------------------------------- #

    def _accept_loop(self) -> None:
        while not self._stop_evt.is_set():
            srv = self._srv
            if srv is None:
                return
            try:
                conn, addr = srv.accept()
            except socket.timeout:
                continue
            except OSError:
                return                          # listener closed: we are done
            # THE CAP USED TO COUNT THE WRONG THING. _clients holds peers that
            # have ALREADY authenticated, so a peer that never finishes the
            # handshake was never counted -- and every accept span a thread that
            # lived for the full NET_AUTH_TIMEOUT_S. Anyone who could reach the
            # port could therefore hold an unbounded number of threads open by
            # connecting and saying nothing, without knowing the token at all.
            # Bounding connections IN THE HANDSHAKE is the check that matters;
            # the authenticated cap below stays as the fan-out bound it always
            # was.
            with self._lock:
                too_many = (len(self._clients) >= NET_MAX_CLIENTS
                            or self._pending >= NET_MAX_PENDING)
                if not too_many:
                    self._pending += 1
            if too_many:
                log(f"TCP refused {addr[0]}: {len(self._clients)} linked, "
                    f"{self._pending} in handshake")
                self._shutdown(conn)
                continue
            t = threading.Thread(target=self._serve, args=(conn, addr),
                                 name="net-client", daemon=True)
            t.start()
            with self._lock:
                self._threads = [x for x in self._threads if x.is_alive()]
                self._threads.append(t)

    def _authenticate(self, conn: socket.socket, peer: str) -> bool:
        """Nonce challenge / HMAC response. False = reject (caller closes)."""
        nonce = secrets.token_hex(16)
        expect = hmac.new(self._token, nonce.encode("ascii"),
                          "sha256").hexdigest()
        try:
            # One budget for the entire handshake, wall-clock, from before the
            # challenge goes out. See _read_line_blocking().
            deadline = time.monotonic() + NET_AUTH_TIMEOUT_S
            conn.settimeout(NET_AUTH_TIMEOUT_S)
            conn.sendall(f"C|{nonce}\n".encode("ascii"))
            reply = self._read_line_blocking(conn, deadline=deadline)
        except (OSError, socket.timeout):
            log(f"TCP {peer}: handshake timed out")
            return False
        if reply is None or not reply.startswith("A|"):
            log(f"TCP {peer}: bad handshake {reply!r}")
            return False
        # A device that knows it has no token says so, rather than hanging up and
        # leaving us to report "bad handshake None" -- which reads like a crash
        # or a network fault and sends you looking in the wrong place entirely.
        # It is the commonest wireless failure by far, because it is what a
        # cleared token looks like, so it gets the one message that says exactly
        # what to do about it.
        if reply.strip().upper() == "A|NOTOKEN":
            self._log_no_token(peer)
            try:
                conn.sendall(b"A|NO\n")
            except OSError:
                pass
            return False
        # compare_digest keeps the comparison time independent of how much of
        # the MAC an attacker guessed right.
        if not hmac.compare_digest(reply[2:].strip().lower(), expect):
            log(f"TCP {peer}: token rejected")
            try:
                conn.sendall(b"A|NO\n")
            except OSError:
                pass
            time.sleep(0.5)                     # take the shine off brute force
            return False
        try:
            conn.sendall(b"A|OK\n")
        except OSError:
            return False
        return True

    def _log_no_token(self, peer: str) -> None:
        """The actionable message, throttled.

        The device redials every couple of seconds, so an unthrottled message
        would bury the log in copies of itself -- which is its own kind of
        useless, and exactly what `bad handshake None` was already doing."""
        now = time.time()
        if now - self._no_token_logged < NO_TOKEN_LOG_GAP_S:
            return
        self._no_token_logged = now
        path = os.path.expanduser(os.environ.get("CLAUDE_MATE_TOKEN_FILE",
                                                 DEFAULT_TOKEN_FILE))
        log(f"TCP {peer}: THE DEVICE HAS NO TOKEN. Open its wifi setup portal "
            f"(4th button -> MENU -> WI-FI) and paste the token into 'Shared "
            f"token', or send T|<token> over USB.")
        log(f"    this daemon's token is in {path}")

    @staticmethod
    def _read_line_blocking(conn: socket.socket,
                            deadline: Optional[float] = None) -> Optional[str]:
        """One newline-terminated line, bounded by NET_MAX_LINE. None on EOF.

        `deadline` is an absolute time.monotonic() value bounding the WHOLE
        line, and the handshake passes one.

        WHY A DEADLINE AND NOT JUST A SOCKET TIMEOUT. This reads one byte at a
        time, and a socket timeout re-arms on every successful recv -- so it
        bounds the gap between bytes, not the read. A peer dripping one byte
        every four seconds beat a five-second timeout indefinitely: 512 bytes
        of drip is roughly forty minutes of held thread, per connection, for an
        attacker who never has to know the token. Bounding how MANY such peers
        there can be (NET_MAX_PENDING) does not help if each one holds its slot
        for forty minutes -- together they simply keep the real device out.
        """
        buf = bytearray()
        while len(buf) < NET_MAX_LINE:
            if deadline is not None:
                remaining = deadline - time.monotonic()
                if remaining <= 0:
                    raise socket.timeout("handshake deadline exceeded")
                conn.settimeout(remaining)
            chunk = conn.recv(1)
            if not chunk:
                return None
            if chunk in (b"\n", b"\r"):
                if not buf:
                    continue                    # tolerate CRLF / blank lines
                break
            buf += chunk
        return buf.decode("ascii", errors="replace").strip()

    def _serve(self, conn: socket.socket, addr) -> None:
        peer = f"{addr[0]}:{addr[1]}"
        # try/finally around the handshake ALONE: the slot being released here
        # is the pre-auth one, and holding it for the lifetime of an established
        # link would mean four healthy devices exhausted the handshake budget
        # and nothing could ever connect again.
        try:
            ok = self._authenticate(conn, peer)
        finally:
            with self._lock:
                self._pending = max(0, self._pending - 1)
        if not ok:
            self._shutdown(conn)
            return
        try:
            # Keepalives so a device that drops off WiFi without a FIN is
            # eventually reaped even if we happen never to write to it.
            conn.setsockopt(socket.SOL_SOCKET, socket.SO_KEEPALIVE, 1)
            conn.settimeout(None)               # blocking reads from here on
        except OSError:
            pass
        with self._lock:
            self._clients.append(conn)
        log(f"TCP device connected: {peer}")
        try:
            while not self._stop_evt.is_set():
                try:
                    line = self._read_line_blocking(conn)
                except (OSError, socket.timeout):
                    break
                if line is None:
                    break                       # clean EOF
                if line:
                    self._rx.put(line)
        finally:
            with self._lock:
                if conn in self._clients:
                    self._clients.remove(conn)
            self._shutdown(conn)
            log(f"TCP device disconnected: {peer}")

    # ---- the link surface ------------------------------------------------- #

    def has_clients(self) -> bool:
        with self._lock:
            return bool(self._clients)

    def write_line(self, line: str) -> bool:
        """Fan out to every client. True if at least one took the bytes."""
        data = (line.rstrip("\n") + "\n").encode("ascii", errors="replace")
        with self._lock:
            targets = list(self._clients)
        if not targets:
            return False
        dead: List[socket.socket] = []
        ok = False
        for c in targets:
            try:
                c.sendall(data)
                ok = True
            except OSError:
                dead.append(c)
        if dead:
            with self._lock:
                for c in dead:
                    if c in self._clients:
                        self._clients.remove(c)
            for c in dead:
                self._shutdown(c)               # its reader thread unblocks
        return ok


class LinkHub:
    """One device link made of a USB serial port plus any wireless transports.

    Presents exactly the surface the rest of the daemon already used on
    SerialLink (is_open / ensure_open / write_line / read_line / close), so
    Screen, ButtonReader and SerialMaintainer are untouched.

    Frames go to EVERY transport; incoming lines from any of them arrive on one
    queue. A dedicated pump moves serial input onto that queue so a wireless
    button press is never stuck behind a blocking serial read.

    The wireless ones are held as a list rather than as named fields because
    there are two of them now (a TCP listener and a BLE central) and there is
    nothing this class needs to know about either beyond has_clients /
    write_line / stop. Both are optional and either can be absent: --tcp alone,
    --ble alone, both, or a device on a cable and nothing else.
    """

    def __init__(self, serial_link: SerialLink,
                 wireless: List[Any],
                 rx: "queue.Queue[str]") -> None:
        self._serial = serial_link
        self._wireless = [w for w in wireless if w is not None]
        self._rx = rx
        self._stop_evt = threading.Event()
        self._pump = threading.Thread(target=self._pump_serial,
                                      name="serial-rx-pump", daemon=True)
        self._pump.start()

    def _pump_serial(self) -> None:
        while not self._stop_evt.is_set():
            if not self._serial.is_open():
                self._stop_evt.wait(0.2)        # nothing to read; don't spin
                continue
            line = self._serial.read_line()     # bounded by the read timeout
            if line:
                self._rx.put(line)

    # ---- the link surface ------------------------------------------------- #

    def _any_wireless(self) -> bool:
        return any(w.has_clients() for w in self._wireless)

    def is_open(self) -> bool:
        """Is ANY device reachable? A wireless client counts."""
        return self._serial.is_open() or self._any_wireless()

    def ensure_open(self) -> bool:
        """Try to (re)open serial; a connected wireless device also counts as
        up, so startup does not report "no device" when only the radio is in
        use."""
        opened = self._serial.ensure_open()
        return opened or self._any_wireless()

    # The USB port, asked about on its OWN terms. is_open()/ensure_open() above
    # answer "is anything reachable", which is right for startup but WRONG for
    # the maintainer: with a wireless device connected they return True while
    # the serial port is shut, so a Nano that drops -- or is plugged in later --
    # would never be reopened and would sit on NO LINK forever.
    def provision_if_ours(self) -> None:
        """Forward to the serial link. See SerialLink.provision_if_ours().

        The ButtonReader holds whatever `link` main() built -- this hub whenever
        a radio is enabled -- so a serial-only method that is not forwarded here
        is simply never called, silently. That is what happened: the token push
        waited for a `K` that reached a hub with no way to pass it on.
        """
        self._serial.provision_if_ours()

    def serial_is_open(self) -> bool:
        return self._serial.is_open()

    def ensure_serial_open(self) -> bool:
        return self._serial.ensure_open()

    def write_line(self, line: str) -> bool:
        # Deliberately not short-circuiting: every connected device must get
        # every frame, so every write runs. A `or` chain would stop at the first
        # transport that took the bytes and leave a second device showing a
        # frame from a minute ago.
        ok = self._serial.write_line(line)
        for w in self._wireless:
            ok = w.write_line(line) or ok
        return ok

    def read_line(self) -> Optional[str]:
        try:
            return self._rx.get(timeout=0.5)
        except queue.Empty:
            return None

    def close(self) -> None:
        self._stop_evt.set()
        for w in self._wireless:
            w.stop()
        self._serial.close()


# Anything the rest of the daemon needs from a device link.
Link = Union[SerialLink, LinkHub]


def _run_quiet(argv: List[str], timeout: float = 3.0) -> str:
    """Run a read-only system tool and return stdout, or "" if anything fails."""
    try:
        out = subprocess.run(argv, stdout=subprocess.PIPE,
                             stderr=subprocess.DEVNULL, timeout=timeout)
    except (OSError, subprocess.SubprocessError):
        return ""
    return out.stdout.decode("utf-8", "replace")


# PROC FIRST, THEN THE BSD TOOLS. This is a macOS product, but the daemon is
# plain Python that people run and test on Linux -- CI does, on every push --
# and `route -n get default` is a BSD-ism that Linux's route(8) does not
# understand. It failed the way an unparseable answer always does: silently, as
# "no gateway", which the gate correctly read as "unidentifiable network" and
# correctly refused to listen on. Correct, and completely useless: the wireless
# link simply never came up, with a security feature quietly holding the door.
# Reading /proc costs no subprocess at all, so it is also the faster path where
# it exists.
def _gateway_from_proc() -> Optional[str]:
    """Linux: the default route's gateway from /proc/net/route, or None."""
    try:
        with open("/proc/net/route", encoding="ascii") as fh:
            next(fh, None)                       # header
            for line in fh:
                parts = line.split()
                if len(parts) < 3 or parts[1] != "00000000":
                    continue                     # not the default route
                # Little-endian hex, so 010011AC is 172.17.0.1.
                raw = int(parts[2], 16)
                if not raw:
                    continue
                return ".".join(str((raw >> (8 * i)) & 0xFF) for i in range(4))
    except (OSError, ValueError):
        pass
    return None


def _mac_from_proc(gw: str) -> Optional[str]:
    """Linux: the gateway's MAC from /proc/net/arp, or None if not cached."""
    try:
        with open("/proc/net/arp", encoding="ascii") as fh:
            next(fh, None)                       # header
            for line in fh:
                parts = line.split()
                if len(parts) >= 4 and parts[0] == gw:
                    return normalise_mac(parts[3])
    except OSError:
        pass
    return None


def default_gateway() -> Optional[str]:
    """The default route's gateway IP, or None when there is no route at all."""
    gw = _gateway_from_proc()
    if gw:
        return gw
    for line in _run_quiet(["route", "-n", "get", "default"]).splitlines():
        line = line.strip()
        if line.startswith("gateway:"):
            gw = line.split(":", 1)[1].strip()
            return gw or None
    return None


def current_network_id() -> Optional[str]:
    """A stable fingerprint for the network this Mac is on, or None if offline.

    The gateway's MAC address, normalised. See the note at TRUSTED_FILE for why
    it is the MAC and not the SSID or the subnet.
    """
    gw = default_gateway()
    if not gw:
        return None
    from_proc = _mac_from_proc(gw)
    if from_proc:
        return from_proc
    # `arp -n 192.168.68.1` -> "? (192.168.68.1) at 60:32:b1:1a:ee:40 on en0 ..."
    # ...or "? (192.168.68.1) -- no entry" when the cache is cold, which is not
    # an error: it happens for a second or two after joining, and the caller
    # simply re-checks on the next poll.
    out = _run_quiet(["arp", "-n", gw])
    if " at " not in out:
        return None
    mac = out.split(" at ", 1)[1].split()[0]
    return normalise_mac(mac)


def normalise_mac(mac: str) -> Optional[str]:
    """Lowercase, zero-padded, colon-separated -- or None if it is not a MAC.

    macOS `arp` drops leading zeros ("0:1a:2b:3c:4d:5e"), so the SAME network
    fingerprints two different ways depending on which octets happen to be
    small. Comparing the raw strings would quietly stop matching the file the
    user trusted, which presents as "my trusted network is not trusted any
    more" -- so normalise on the way in AND on the way out.
    """
    parts = mac.strip().lower().split(":")
    if len(parts) != 6:
        return None
    try:
        return ":".join(f"{int(p, 16):02x}" for p in parts)
    except ValueError:
        return None


def trusted_networks() -> Dict[str, str]:
    """Trusted gateway MAC -> the label the user gave it. Missing file = {}."""
    path = os.path.expanduser(os.environ.get("CLAUDE_MATE_TRUSTED_FILE",
                                             TRUSTED_FILE))
    out: Dict[str, str] = {}
    try:
        with open(path, encoding="utf-8") as fh:
            for line in fh:
                line = line.split("#", 1)[0].strip()
                if not line:
                    continue
                mac, _, label = line.partition(" ")
                norm = normalise_mac(mac)
                if norm:
                    out[norm] = label.strip() or "(unnamed)"
    except OSError:
        pass
    return out


def trust_network(net_id: str, label: str) -> bool:
    """Add a network to the trusted file. True if it was written."""
    path = os.path.expanduser(os.environ.get("CLAUDE_MATE_TRUSTED_FILE",
                                             TRUSTED_FILE))
    norm = normalise_mac(net_id)
    if not norm:
        return False
    if norm in trusted_networks():
        return True
    try:
        os.makedirs(os.path.dirname(path), exist_ok=True)
        # 0600: this file decides who the daemon will talk to. It is not a
        # secret, but it is a policy, and a policy anything can append to is
        # not one.
        fd = os.open(path, os.O_WRONLY | os.O_CREAT | os.O_APPEND, 0o600)
        with os.fdopen(fd, "a", encoding="utf-8") as fh:
            fh.write(f"{norm} {label}\n")
        return True
    except OSError as exc:
        log(f"could not write {path}: {exc}")
        return False


class NetworkGate(threading.Thread):
    """Keeps the TCP listener and the mDNS advert off untrusted networks.

    Polls which network we are on and opens or closes the listener to match.
    Runs even when the answer never changes, because the interesting case is
    precisely the one nobody is watching: the laptop that was closed at home and
    opened somewhere else.

    TRUST ON FIRST USE, ONCE. An upgrade must not silently disconnect a device
    that worked yesterday, so if the trusted file does not exist yet the first
    network seen is adopted and loudly logged. That is never worse than the old
    behaviour -- which was to listen on every network without asking -- and from
    the second network onwards it is strictly better. `claude-mate trust --list`
    shows what was adopted and `--remove` undoes it.
    """

    def __init__(self, net: "NetLink", mdns: Optional["MdnsAdvertiser"],
                 poll_s: float = NET_GATE_POLL_S) -> None:
        super().__init__(name="net-gate", daemon=True)
        self._net = net
        self._mdns = mdns
        self._poll_s = poll_s
        self._stop_evt = threading.Event()
        self._open = False
        self._last_id: Optional[str] = ""      # "" = nothing evaluated yet

    def is_open(self) -> bool:
        return self._open

    def stop(self) -> None:
        self._stop_evt.set()

    def run(self) -> None:
        while not self._stop_evt.is_set():
            try:
                self.evaluate()
            except Exception as exc:                        # noqa: BLE001
                # A gate that crashes must fail CLOSED, and must say so. The
                # alternative -- a dead thread and a listener nobody is
                # re-evaluating -- is the one outcome worse than either state.
                log(f"network gate error ({exc}); closing the listener")
                self._apply(False, "gate error")
            self._stop_evt.wait(self._poll_s)

    def evaluate(self) -> None:
        net_id = current_network_id()
        if net_id is None:
            self._apply(False, "no network")
            self._last_id = None
            return
        known = trusted_networks()
        if not known and not os.path.exists(
                os.path.expanduser(os.environ.get("CLAUDE_MATE_TRUSTED_FILE",
                                                  TRUSTED_FILE))):
            if trust_network(net_id, "first-seen"):
                log(f"trusting the network you are on ({net_id}) -- first run. "
                    f"`claude-mate trust --list` to review, `--remove` to undo.")
                known = trusted_networks()
        if net_id in known:
            self._apply(True, f"{known[net_id]} ({net_id})")
        else:
            self._apply(False, f"untrusted network {net_id}")
        self._last_id = net_id

    def _apply(self, want_open: bool, why: str) -> None:
        if want_open == self._open:
            return
        self._open = want_open
        if want_open:
            if self._net.start():
                log(f"TCP listener open: {why}")
                if self._mdns:
                    self._mdns.start()
            else:
                self._open = False
        else:
            self._net.stop()
            if self._mdns:
                self._mdns.stop()
            log(f"TCP listener closed: {why}. "
                f"`claude-mate trust` to allow this network.")


class MdnsAdvertiser:
    """Advertises the TCP listener as _claudemate._tcp via macOS `dns-sd`.

    Uses the system tool rather than a Bonjour library so the daemon keeps its
    single third-party dependency (pyserial). Best-effort: no dns-sd, no
    advertisement -- the device can still be pointed at a host by hand.
    """

    def __init__(self, port: int) -> None:
        self._port = port
        self._proc: Optional[subprocess.Popen] = None

    def start(self) -> None:
        if not _which("dns-sd"):
            log("dns-sd not found; skipping mDNS advertisement")
            return
        try:
            self._proc = subprocess.Popen(
                ["dns-sd", "-R", MDNS_NAME, MDNS_SERVICE, "local",
                 str(self._port)],
                stdout=subprocess.DEVNULL, stderr=subprocess.DEVNULL,
                stdin=subprocess.DEVNULL,
            )
            log(f"advertising {MDNS_NAME} {MDNS_SERVICE} on port {self._port}")
        except OSError as exc:
            log(f"mDNS advertisement failed: {exc}")

    def stop(self) -> None:
        proc, self._proc = self._proc, None
        if proc is None:
            return
        try:
            proc.terminate()
            proc.wait(timeout=1.0)
        except Exception:
            try:
                proc.kill()
            except Exception:
                pass


# --------------------------------------------------------------------------- #
# Screen: composes the single frame and owns selection + LED state.
# --------------------------------------------------------------------------- #


def _fmt_time(seconds: float) -> str:
    """Format seconds as mm:ss, or h:mm for >= 1 hour. Always <= 5 chars."""
    seconds = int(max(0, seconds))
    if seconds >= 3600:
        h = seconds // 3600
        m = (seconds % 3600) // 60
        return f"{h}:{m:02d}"
    m = seconds // 60
    s = seconds % 60
    return f"{m:02d}:{s:02d}"


def _sanitize(text: str) -> str:
    """Strip protocol-corrupting characters from a display string: the field
    separator and ALL C0 control chars + DEL (an embedded NUL or newline would
    otherwise wedge the firmware tokenizer on every frame for that subject).
    Non-ASCII is left to write_line's ascii/replace ('?'), which is 1-for-1 so
    field counts and length budgets hold."""
    text = (text or "").replace("|", "/")
    return "".join(ch if (ch >= " " and ch != "\x7f") else " " for ch in text)


def _fit_meta(model: str, effort: str, width: int) -> str:
    """Best-fit 'model effort' into `width` chars, degrading gracefully:
    full model+effort -> first-word model+effort -> effort -> model, truncated."""
    model = _sanitize(model).strip()
    effort = _sanitize(effort).strip()
    cands: List[str] = []
    if model and effort:
        cands = [f"{model} {effort}", f"{model.split()[0]} {effort}", effort]
    elif model:
        cands = [model, model.split()[0]]
    elif effort:
        cands = [effort]
    for c in cands:
        if len(c) <= width:
            return c
    return cands[-1][:width] if cands else ""


def _wrap2(text: str) -> Tuple[str, str]:
    """Word-wrap a short message into the two 21-char rows a notice gets.

    Words first, because breaking a domain name across rows makes the thing you
    are being asked to notice unreadable. A word longer than a row is cut rather
    than allowed to swallow both -- overflow ends in an ellipsis so a truncated
    message never reads as a complete one that happens to be odd."""
    rows, i = ["", ""], 0
    for w in _sanitize(text).split():
        w = w[:ROW_CHARS]
        cand = f"{rows[i]} {w}".strip()
        if len(cand) <= ROW_CHARS:
            rows[i] = cand
        elif i == 0:
            i = 1
            rows[i] = w
        else:                                     # '+' = "and more", the same
            rows[1] = rows[1][:ROW_CHARS - 1] + "+"   # mark the fleet strip uses
            break
    return (rows[0], rows[1])


def _display_names(sessions: List[Session]) -> Dict[str, str]:
    """Map session key -> display name truncated to ROW_CHARS (the full size-1
    row now), disambiguating collisions (sibling dirs with a long common prefix)
    with a middle squeeze: first 9 chars + '~' + last 10 chars."""
    out: Dict[str, str] = {}
    plain: Dict[str, List[Session]] = {}
    for s in sessions:
        nm = _sanitize(s.name).strip() or "?"
        t = nm[:ROW_CHARS]
        plain.setdefault(t, []).append(s)
        out[s.key] = t
    for t, group in plain.items():
        if len(group) < 2:
            continue
        # Only a real collision if the FULL names differ (identical basenames
        # cannot be disambiguated by truncation at all).
        fulls = {g.name for g in group}
        if len(fulls) < 2:
            continue
        for g in group:
            nm = _sanitize(g.name).strip()
            if len(nm) > ROW_CHARS:
                out[g.key] = nm[:9] + "~" + nm[-10:]
    return out


class Screen:
    """Owns everything the device shows: the selection, the pre-rendered frame,
    and the LED loop tracker."""

    def __init__(self, link: Link, registry: Registry,
                 sound: bool = False) -> None:
        self._link = link
        self._reg = registry
        self._lock = threading.Lock()
        # Selection: a session KEY, or None meaning "the queue head". Tracked
        # by key so re-sorts never move the subject out from under the cursor.
        # STICKY: only PREV/NEXT/GO (and the head fallback when the selected
        # session vanishes) ever move it -- the screen never switches tabs on
        # its own.
        self._sel_key: Optional[str] = None
        # Last frame actually sent (dedup) + the key of the subject CURRENTLY
        # ON THE GLASS. A GO/ACK press acts on exactly this key (WYSIWYG), so
        # the raised terminal always matches the name the user is looking at.
        self._last_frame = ""
        self._shown_key: Optional[str] = None
        # FOLLOW mode: when on, PREV/NEXT auto-raise the selected terminal. The
        # active tab's fleet letter is boxed either way; the box is FILLED while
        # following (the on-screen "switch"), an outline when not.
        self._follow = False
        # LED loop tracker: what continuous loop the firmware is playing
        # ("ERROR"/"INPUT"/"DONE"/None); V| is (re)sent only when it changes.
        self._loop_kind: Optional[str] = _LOOP_UNSET
        # Alert sound (macOS). Rides the SAME transition as the LED rather than
        # having a policy of its own -- one truth, three renderings (rhythm,
        # colour, sound), which is the rule the S3's colour LED already follows.
        self._sound = sound
        self._last_sound_at = 0.0
        self._last_sfx_at   = 0.0
        self.on_handshake_extra = None   # re-assert edge-driven device state
        # A transient message across the middle two rows: (text, expires_at).
        # An ACTIONS-sheet verb can fail for ordinary reasons -- the session is
        # already on that account, it has said nothing worth carrying yet -- and
        # the wrapper answers every one of them in words. Those words used to go
        # to the log and nowhere else, which from arm's length is exactly what a
        # dead button looks like: the fix for "I pressed it and nothing
        # happened" is not to press harder, it is to say what happened. Rendered
        # by the daemon into the existing frame, so it costs no firmware change
        # and works on a device that is already flashed.
        self._notice: Optional[Tuple[str, float]] = None
        # Rendered lazily-but-once at construction: eight short WAVs, well
        # under a tenth of a second of work, and doing it here means the
        # first jump of the first run is not the one that pays for it.
        self._sfx = sfx_build_cache() if sys.platform == "darwin" else {}

    # ---- transient messages ----------------------------------------------- #

    def notice(self, text: str, secs: float = NOTICE_S) -> None:
        """Say something on the glass for a few seconds.

        Set OUTSIDE the lock-holding path and pushed immediately: a message
        about a press has to land while the finger is still near the button, not
        on whatever tick comes next. A timer forces one more refresh when it
        expires, otherwise a device with nothing else happening would keep the
        stale message until the next state change -- which, for an idle fleet at
        2am, could be hours."""
        with self._lock:
            self._notice = (text, time.monotonic() + secs)
        self.refresh(force=True)
        t = threading.Timer(secs + 0.05, self.refresh, kwargs={"force": True})
        t.daemon = True
        t.start()

    def _notice_rows(self) -> Optional[Tuple[str, str]]:
        """The live notice as two rows, or None. Expiry is checked HERE rather
        than by the timer, so a frame composed for any other reason after the
        deadline also drops it."""
        if self._notice is None:
            return None
        text, until = self._notice
        if time.monotonic() >= until:
            self._notice = None
            return None
        return _wrap2(text)

    # ---- selection -------------------------------------------------------- #

    def _subject(self, queue: List[Session]) -> Optional[Session]:
        """The session the screen shows: the selected key if it still exists,
        else the queue head."""
        if not queue:
            return None
        key = self._sel_key
        if key is not None:
            for s in queue:
                if s.key == key:
                    return s
        return queue[0]

    def nav(self, delta: int) -> None:
        """PREV/NEXT: move the selection by `delta` in queue order (wraps)."""
        with self._lock:
            queue = self._reg.queue()
            if not queue:
                return
            cur = self._subject(queue)
            idx = 0
            for i, s in enumerate(queue):
                if cur is not None and s.key == cur.key:
                    idx = i
                    break
            nxt = queue[(idx + delta) % len(queue)]
            self._sel_key = nxt.key
        self.refresh()

    def select_by(self, want: str) -> Optional[str]:
        """Select a session by queue index or by name. Returns the name, or None.

        The device has no equivalent -- it walks there with PREV/NEXT -- but a
        terminal that can print the whole queue at once should be able to point
        at a row instead of stepping to it. The index is into the SAME queue the
        snapshot prints, so what you read is what you get.

        Name matching is exact-first, then unique prefix, then unique substring.
        AMBIGUITY IS A REFUSAL rather than a guess: this moves what GO acts on,
        and picking the wrong session is the one mistake that costs you the
        window you were trying to raise.
        """
        want = want.strip()
        if not want:
            return None
        queue = self._reg.queue()
        if not queue:
            return None
        pick = None
        if want.isdigit():
            i = int(want)
            if 0 <= i < len(queue):
                pick = queue[i]
        if pick is None:
            for pred in (lambda s: s.name == want,
                         lambda s: s.name.lower() == want.lower(),
                         lambda s: s.name.lower().startswith(want.lower()),
                         lambda s: want.lower() in s.name.lower()):
                hits = [s for s in queue if pred(s)]
                if len(hits) == 1:
                    pick = hits[0]
                    break
                if len(hits) > 1:
                    return None            # ambiguous: refuse, do not guess
        if pick is None:
            return None
        with self._lock:
            self._sel_key = pick.key
        self.refresh()
        return pick.name

    def stay_on(self, sess: Optional[Session]) -> None:
        """After a GO/ACK: pin the selection to the session the press acted on
        (and redraw, e.g. so its flash stops) -- the device stays on it."""
        if sess is None:
            return
        with self._lock:
            self._sel_key = sess.key
        self.refresh()

    def toggle_follow(self) -> bool:
        """Flip FOLLOW mode. Returns the new state. Reached by a GO
        double-click, or by holding the 4-button device's ACK button."""
        with self._lock:
            self._follow = not self._follow
            state = self._follow
        self.refresh()          # redraw so the switch box fills/empties
        return state

    def is_follow(self) -> bool:
        with self._lock:
            return self._follow

    def current_shown(self) -> Optional[Session]:
        """The session whose frame is on the glass right now (for FOLLOW's
        auto-raise), or None."""
        with self._lock:
            key = self._shown_key
            if key is None:
                return None
            for s in self._reg.queue():
                if s.key == key:
                    return s
            return None

    def resolve_press_target(self) -> Optional[Session]:
        """The session a GO/ACK press applies to: EXACTLY the one whose frame is
        on the glass (WYSIWYG). Never a freshly recomputed head -- so a press
        can only ever act on the name the user is actually looking at. Falls
        back to the queue head only if the shown session has vanished."""
        with self._lock:
            queue = self._reg.queue()
            if self._shown_key is not None:
                for s in queue:
                    if s.key == self._shown_key:
                        return s
            return self._subject(queue)         # shown session gone -> head

    # ---- frame composition -------------------------------------------------- #

    def _compose(self, queue: List[Session],
                 subject: Optional[Session]) -> Tuple[str, Optional[str], bool]:
        """Build the F| line for the current state:
            F|<flags>|<sel>|<r0>|<r1>|<r2>|<r3>
        with four size-1 rows (r0 name / r1 state+time + account / r2
        model+effort + remaining-limit chip / r3 position + fleet letters).
        `flags` is a bitfield
        (bit0 = flash the name, bit1 = FOLLOW mode -> draw the play marker);
        `sel` is the character column WITHIN r3 of the active tab's fleet
        letter to box (-1 = none). Returns (line, subject_key, flash). r3 is
        LAST and may contain literal '|' (the firmware stops tokenizing at the
        6th bar and takes the rest verbatim), which is what lets the strip use
        '|' as its visual divider."""
        follow = self._follow
        note = self._notice_rows()
        if subject is None:
            if note:
                return (f"F|0|-1|MATE|{note[0]}|{note[1]}|", None, False)
            return (f"F|{2 if follow else 0}|-1|MATE|no sessions||", None, False)

        names = _display_names(queue)
        r0 = names.get(subject.key, "?")[:ROW_CHARS]

        tag = STATE_TAG.get(subject.state, "IDLE")
        t = _fmt_time(subject.display_seconds())
        r1 = f"{tag:<4}  {t}"[:ROW_CHARS]
        # Account the session runs as (PTY wrapper), right-aligned on the
        # state row with a >= 2-space gap; truncated to what fits. FOLLOW's
        # play triangle is drawn over the last two columns of this row, so
        # those stay blank while following (the account shifts/truncates left
        # instead of being overdrawn).
        acct = _sanitize(subject.account).strip()
        width = ROW_CHARS - (2 if follow else 0)
        room = width - len(r1) - 2
        if acct and room >= 2:
            r1 += acct[:room].rjust(width - len(r1))

        # Remaining-limit chip (e.g. "5h82%"), right-aligned on the meta row;
        # model+effort best-fit into what the chip leaves (>= 2-space gap).
        lim = _sanitize(subject.limit).strip()[:8]
        if lim:
            left = _fit_meta(subject.model, subject.effort,
                             ROW_CHARS - len(lim) - 2)
            r2 = (left + lim.rjust(ROW_CHARS - len(left)))[:ROW_CHARS]
        else:
            r2 = _fit_meta(subject.model, subject.effort, ROW_CHARS)

        pos = 1
        for i, s in enumerate(queue):
            if s.key == subject.key:
                pos = i + 1
                break
        head = f"{pos}/{len(queue)} "
        room = ROW_CHARS - len(head)
        # One letter per session, SPACE-separated (no '|' bars -- the active-tab
        # square marks which is which; the space gives the highlight rectangle
        # room to centre the letter). An UNACKNOWLEDGED alert's letter is sent
        # LOWERCASE so the firmware BLINKS it -- you can see at a glance which
        # tabs still need acknowledging (they stop as you ack them).
        letters = []
        for s in queue:
            ltr = STATE_LETTER.get(s.state, "I")
            letters.append(ltr.lower() if s.unacked_alert() else ltr)
        strip = " ".join(letters)
        if len(strip) > room:
            strip = strip[:max(0, room - 1)] + "+"
        r3 = head + strip
        # Column of the active tab's letter within r3 (letters sit at even
        # strip offsets: 0,2,4,...; spaces at the odds). -1 if it fell past a
        # truncation.
        sel = len(head) + 2 * (pos - 1)
        if sel >= len(r3) or not r3[sel].isalpha():
            sel = -1

        flash = subject.unacked_alert()
        flags = (1 if flash else 0) | (2 if follow else 0)
        # A notice takes the middle two rows and leaves r0 and r3 alone: you
        # keep the name of the session it is ABOUT, and the fleet strip that
        # tells you nothing has moved underneath. Losing state+time and
        # model+effort for four seconds costs nothing; losing which session is
        # being talked about would make the message ambiguous.
        if note:
            r1, r2 = note
        line = f"F|{flags}|{sel}|{r0}|{r1}|{r2}|{r3}"
        return (line, subject.key, flash)

    def refresh(self, force: bool = False) -> None:
        """Re-compose the frame and send it if the bytes changed (or `force`).

        The queue snapshot is taken INSIDE the Screen lock so snapshot-time and
        commit-time are ordered -- a preempted caller can never commit a stale
        frame over a newer one (Screen -> Registry lock nesting is safe: the
        registry never takes the Screen lock)."""
        with self._lock:
            queue = self._reg.queue()
            subject = self._subject(queue)
            if subject is not None:
                # The screen NEVER switches tabs on its own: anchor the
                # selection to whatever is rendered (the first tab when nothing
                # was ever selected, the head fallback after the selected
                # session vanished), so it stays put until the user navigates.
                # Alerts elsewhere signal via the LED and their blinking fleet
                # letters only.
                self._sel_key = subject.key
            line, key, flash = self._compose(queue, subject)
            changed = (line != self._last_frame)
            if changed or force:
                if self._link.write_line(line):
                    self._last_frame = line
                    self._shown_key = key

    # ---- LED ---------------------------------------------------------------- #

    def sync_led(self) -> None:
        """Single source of truth for the indicator LED. Reads the most-urgent
        unacknowledged alert and drives the firmware loop:

          * error / waiting / done -> a CONTINUOUS loop (V|ERROR / V|INPUT /
            V|DONE); the firmware repeats it until V|OFF.
          * nothing -> V|OFF, silence.

        The truth read, the dedup check, the write, and the tracker commit all
        happen under ONE lock hold, so concurrent callers can never invert the
        LED state with a stale snapshot. The commit is gated on a SUCCESSFUL
        write -- a failed write (port momentarily closed) leaves the tracker
        stale so the next tick retries."""
        with self._lock:
            top = self._reg.top_alert()
            kind = LOOP_KIND.get(top.state) if top is not None else None
            if kind == self._loop_kind:
                return
            line = f"V|{kind}" if kind else "V|OFF"
            if not self._link.write_line(line):
                return                        # keep tracker stale -> retry next tick
            self._loop_kind = kind
            if kind:
                log(f"LED: loop {kind} until acknowledged")
            self._play_alert(kind)

    def set_sound(self, on: bool) -> None:
        """Enable/disable the macOS alert sound. Called from the device."""
        with self._lock:
            if self._sound == on:
                return
            self._sound = on
        log(f"sound: {'on' if on else 'off'} (set from the device)")

    def _play_alert(self, kind: Optional[str]) -> None:
        """Play one sound for an alert-class transition. Never blocks, never
        raises, and never becomes load-bearing.

        Deliberately ONE-SHOT, where the LED loops until acknowledged. Light is
        ignorable and a beep is not: a sound that repeated until you dealt with
        it would be a smoke alarm, and would get the whole feature switched off
        within a day. The LED carries the persistent state; sound only marks the
        moment it changed.

        Called with self._lock held, so it must not do anything that can wait --
        Popen returns as soon as the child is spawned, and the child is fully
        detached (nothing ever reaps it, so stdio goes to /dev/null and we let
        it exit on its own)."""
        if not (self._sound and kind):
            return
        if sys.platform != "darwin":
            return
        now = time.time()
        # A session flapping error -> waiting -> error would otherwise stack up
        # overlapping afplay processes. The LED's dedup does not cover this: the
        # kind genuinely changes each time, so the transition is real.
        if now - self._last_sound_at < SOUND_MIN_GAP_S:
            return
        name = ALERT_SOUNDS.get(kind)
        if not name:
            return
        path = os.path.join(SOUND_DIR, name)
        try:
            subprocess.Popen(["afplay", path],
                             stdout=subprocess.DEVNULL,
                             stderr=subprocess.DEVNULL,
                             start_new_session=True)
            self._last_sound_at = now
        except Exception as exc:
            # A missing afplay or a renamed system sound must never take the
            # daemon down or stall the alert path -- it is decoration.
            log(f"sound: {exc}")
            self._sound = False        # one complaint, then stop trying

    def play_sfx(self, code: str) -> None:
        """One game sound, from `O|SFX|<code>`. Same contract as _play_alert:
        never blocks, never raises, never becomes load-bearing.

        It keeps its OWN clock rather than sharing _last_sound_at. Sharing would
        break both directions -- the 2 s alert floor would swallow a level's
        worth of jumps, and a run of jumps would suppress a genuine ERROR alert
        that arrived mid-game, which is exactly the alert you would want to hear.
        """
        with self._lock:
            on = self._sound
        if not on or sys.platform != "darwin":
            return
        path = self._sfx.get(code)
        if not path:
            return
        now = time.time()
        if now - self._last_sfx_at < GAME_SOUND_MIN_GAP_S:
            return
        try:
            subprocess.Popen(["afplay", path],
                             stdout=subprocess.DEVNULL,
                             stderr=subprocess.DEVNULL,
                             start_new_session=True)
            self._last_sfx_at = now
        except Exception as exc:
            log(f"game sound: {exc}")

    def start_tick(self) -> None:
        """One-shot START blink (a job (re)started). The caller fires this only
        when nothing needs the human, so it never interrupts an alert loop."""
        self._link.write_line("V|START")
        with self._lock:
            self._play_alert("START")

    # ---- lifecycle ------------------------------------------------------------ #

    def resend_full_state(self) -> None:
        """On handshake (H) / reconnect: push the current frame AND re-arm the
        LED from scratch.

        A handshake means the Nano just (re)booted (opening the port resets it,
        and a replug does too) LED-off, having lost any loop it was playing. If
        we kept our loop tracker, `_set_loop` would see the desired loop already
        "sent" and never re-emit it -- so an unacknowledged alert would go
        permanently silent after a routine replug. So we forget the tracker and
        re-drive the LED from the current alert state."""
        log("handshake H -> resending full state")
        with self._lock:
            self._loop_kind = _LOOP_UNSET      # firmware was reset -> forget it
        self.refresh(force=True)
        self.sync_led()
        # Controller mode is edge-driven -- the daemon sends G| only when the
        # grab CHANGES -- so a device that shows up while a page is already
        # holding it would never be told, and would sit in menu semantics
        # wondering why the game felt laggy. Same class of bug as the sound
        # preference, and the same fix: re-assert on every handshake.
        if self.on_handshake_extra is not None:
            try:
                self.on_handshake_extra()
            except Exception as exc:
                log(f"handshake extra: {exc}")

    def notify_change(self) -> None:
        """Called on any registry change: refresh frame + LED."""
        self.refresh()
        self.sync_led()


# --------------------------------------------------------------------------- #
# FOCUS action (raise/activate ONLY -- never collapse/resize/minimize)
# --------------------------------------------------------------------------- #


ACCOUNTS_DIR = os.path.expanduser(
    os.environ.get("CLAUDE_MATE_ACCOUNTS_DIR", "~/.claude-accounts"))
ACCT_MAX = 5                       # what the device's picker can show


def account_profiles(limit: int = ACCT_MAX) -> List[str]:
    """The SAVED logins, in a stable order both ends agree on.

    'default' first -- it is the ~/.claude login, usually the main one, and it
    is not a directory under the profiles root, so listing only that root left
    the device able to switch AWAY from your main account and never back to it.
    The rest are profile directories under ~/.claude-accounts, each holding its
    own credentials, sorted -- so the index the device sends back means the same
    name the daemon sent. An ordering that drifted between the two ends would
    switch you to the wrong account, which is the one mistake this must not make.
    """
    try:
        rest = sorted(d for d in os.listdir(ACCOUNTS_DIR)
                      if os.path.isdir(os.path.join(ACCOUNTS_DIR, d)))
    except OSError:
        rest = []
    names = ["default"] + rest
    return names[:limit] if limit else names


def account_dir(name: str) -> str:
    """A profile's config dir. 'default' is ~/.claude, which is NOT under the
    profiles root -- the same rule claude-mate-switch follows."""
    return (os.path.expanduser("~/.claude") if name == "default"
            else os.path.join(ACCOUNTS_DIR, name))


# What the device was ACTUALLY told, in order. The device answers with an index,
# so the only list that can decode it is the one it was sent -- not a fresh
# listdir at press time. Profiles appear and disappear while the device is
# linked (starting a session on a new name creates one), and a name sorting into
# the middle renumbers every row below it: the device would still be showing the
# old rows and the press would land on the neighbour. Switching to an account
# you did not choose is the one mistake this feature must not make.
_pushed_accounts: List[str] = []
_pushed_lock = threading.Lock()


def set_pushed_accounts(names: List[str]) -> None:
    with _pushed_lock:
        _pushed_accounts[:] = list(names)


def pushed_accounts() -> List[str]:
    with _pushed_lock:
        return list(_pushed_accounts)


_wrap_mod: Any = None


def account_headroom_chip(cfg_dir: str) -> str:
    """A profile's remaining-limit chip ('5h82%'), or '' if unknown.

    Borrowed from the wrapper rather than reimplemented: reading a profile's
    token means knowing that Claude Code keys the Keychain entry as
    "Claude Code-credentials-<sha256(cfg_dir)[:8]>", which was established by
    experiment and is exactly the sort of detail that rots when it is written
    down twice. Any failure is '' -- an unknown limit must never stop the
    picker listing the account.
    """
    global _wrap_mod
    if _wrap_mod is None:
        try:
            import importlib.machinery
            import importlib.util
            path = os.path.join(os.path.dirname(os.path.dirname(
                os.path.abspath(__file__))), "bin", "claude-mate-wrap")
            spec = importlib.util.spec_from_loader(
                "cm_wrap_helpers",
                importlib.machinery.SourceFileLoader("cm_wrap_helpers", path))
            mod = importlib.util.module_from_spec(spec)
            spec.loader.exec_module(mod)
            _wrap_mod = mod
        except Exception as exc:
            log(f"account usage unavailable: {exc}")
            _wrap_mod = False
    if not _wrap_mod:
        return ""
    try:
        tok = _wrap_mod._access_token(cfg_dir)
        if not tok:
            return ""
        return _wrap_mod._format_limit(_wrap_mod._fetch_usage(tok) or {})
    except Exception:
        return ""


def wrapper_ctrl_send(ctrl: str, cmd: str) -> bool:
    """wrapper_ctrl_call, for callers that only care whether it worked."""
    return wrapper_ctrl_call(ctrl, cmd)[0]


def wrapper_ctrl_call(ctrl: str, cmd: str) -> Tuple[bool, str]:
    """Send one command line ('focus') to a PTY wrapper's per-session control
    socket and WAIT for its ack. The wrapper replies in two stages -- 'go' the
    moment it accepts the command (liveness), 'ok' only after its window op
    (osascript) has COMPLETED -- so consecutive focuses apply in press order.
    The first read waits only WRAPPER_LIVE_TIMEOUT_S, so a wedged wrapper
    (stopped process whose socket the kernel still accepts) costs ~1s, while a
    live-but-slow op gets the full WRAPPER_ACK_TIMEOUT_S deadline. Pre-ack
    wrappers close the socket immediately (recv -> EOF), degrading to
    fire-and-forget.

    Returns (ok, why). `why` is the wrapper's own words when it refuses, and
    the caller is expected to SHOW them: a refusal that only reaches the log is
    indistinguishable, from where the user is standing, from a device that
    ignored the press."""
    if not ctrl or not os.path.exists(ctrl):
        return (False, "session is gone")
    try:
        c = socket.socket(socket.AF_UNIX, socket.SOCK_STREAM)
        c.settimeout(2.0)
        c.connect(ctrl)
        # utf-8, not ascii: a command can carry a profile name, and a profile is
        # a directory the user named. `.encode("ascii")` on one with an accent in
        # it raises UnicodeEncodeError -- not an OSError, so it escaped the
        # handler below and killed the calling thread instead of failing the send.
        c.sendall(cmd.encode("utf-8", "replace") + b"\n")
        buf = b""
        try:
            deadline = time.monotonic() + WRAPPER_ACK_TIMEOUT_S
            c.settimeout(WRAPPER_LIVE_TIMEOUT_S)   # a live wrapper 'go's in ms
            # A refusal is read to its NEWLINE, not to the first chunk. Stopping
            # at "buf starts with err" truncated the reason at whatever one recv
            # happened to return -- 64 bytes, mid-word ("...is another organis"),
            # which is fine for a log nobody reads and useless for a message we
            # now put on the glass. 512 to match the wrapper's own recv.
            while not (b"ok" in buf or (buf.startswith(b"err") and b"\n" in buf)):
                chunk = c.recv(512)
                if not chunk:          # EOF: pre-ack wrapper (or already done)
                    break
                buf += chunk
                c.settimeout(max(0.1, deadline - time.monotonic()))
        except socket.timeout:
            # Deliberately NOT a failure. `focus` uses the return value to
            # decide whether to run its own window-raising fallback, and a slow
            # ack from a wrapper that did raise the window would then raise it
            # twice. A timeout means "no answer yet", which is not "refused".
            log(f"wrapper {cmd} ack timeout ({ctrl}); continuing")
        finally:
            c.close()
        # A wrapper that REFUSES says so ('err <why>') rather than closing
        # silently, and the caller must not report the command as done: the
        # device would show a switch that never happened.
        if buf.startswith(b"err"):
            why = buf.decode("utf-8", "replace").strip()[4:] or "no reason given"
            log(f"wrapper refused {cmd!r}: {why}")
            return (False, why)
        return (True, "")
    except OSError as exc:
        log(f"wrapper {cmd} failed ({ctrl}): {exc}")
        return (False, "could not reach the session")


def wrapper_ctrl_screen(ctrl: str) -> Optional[List[str]]:
    """Ask a PTY wrapper for its rendered TUI, for the device's mirror view.

    Length-prefixed ("SCREEN <n>", then n rows, then "ok") rather than read
    until a sentinel: terminal output can contain ANY line, including one that
    is exactly "ok", which would truncate the mirror at an arbitrary point.
    The wrapper closes the connection when done, so this reads to EOF.

    Returns the rows, or None when there is nothing to show -- no wrapper (a
    hook-only session), a dead one, or one predating the mirror command, which
    answers a bare "ok". None is rendered as "no preview", never as a blank
    screen that would look like a session sitting idle.
    """
    if not ctrl or not os.path.exists(ctrl):
        return None
    buf = b""
    try:
        c = socket.socket(socket.AF_UNIX, socket.SOCK_STREAM)
        c.settimeout(WRAPPER_LIVE_TIMEOUT_S)
        c.connect(ctrl)
        c.sendall(b"screen\n")
        deadline = time.monotonic() + WRAPPER_ACK_TIMEOUT_S
        while True:
            chunk = c.recv(8192)
            if not chunk:                      # EOF: the wrapper is done
                break
            buf += chunk
            remaining = deadline - time.monotonic()
            if remaining <= 0:
                break
            c.settimeout(remaining)
        c.close()
    except OSError:
        return None
    lines = buf.decode("utf-8", "replace").split("\n")
    if not lines or not lines[0].startswith("SCREEN "):
        return None                            # pre-mirror wrapper
    try:
        n = int(lines[0].split()[1])
    except (IndexError, ValueError):
        return None
    return lines[1:1 + n]


def focus_session(sess: Optional[Session]) -> None:
    """
    Raise the terminal/editor window of the given session. RAISE ONLY.

    Best: ask the PTY wrapper to raise its own terminal window (un-minimizes +
    activates). Then: the documented VS Code deep link. Fallback: raise the
    VS Code window for the workspace folder.
    """
    if sess is None:
        log("GO pressed but no session to focus")
        return

    log(f"FOCUS -> {sess.name} (sid={sess.sid or '?'}, cwd={sess.cwd or '?'})")

    # --- Best: ask the PTY wrapper to raise its own terminal window ----------
    if sess.focus_ctrl:
        if wrapper_ctrl_send(sess.focus_ctrl, "focus"):
            return
        log("using focus fallback")

    # --- Primary: deep link (hook-based sessions only) ----------------------
    if sess.sid:
        uri = FOCUS_URI_TEMPLATE.format(
            session_id=urllib.parse.quote(sess.sid, safe="")
        )
        try:
            rc = subprocess.run(
                ["open", uri],
                stdout=subprocess.DEVNULL,
                stderr=subprocess.DEVNULL,
                timeout=5,
            ).returncode
            if rc == 0:
                return  # success
            log(f"deep-link open returned {rc}; using fallback")
        except Exception as exc:
            log(f"deep-link open failed: {exc}; using fallback")

    # --- Fallback: raise the VS Code window for the workspace ---------------
    _focus_fallback(sess)


def _focus_fallback(sess: Session) -> None:
    """Raise the VS Code window (best effort). Never raises."""
    cwd = sess.cwd
    # Prefer `code <cwd>` if the CLI is on PATH (focuses an existing window).
    if cwd and _which("code"):
        try:
            subprocess.run(
                ["code", cwd],
                stdout=subprocess.DEVNULL,
                stderr=subprocess.DEVNULL,
                timeout=5,
            )
            return
        except Exception as exc:
            log(f"`code {cwd}` failed: {exc}")

    if cwd:
        try:
            subprocess.run(
                ["open", "-a", "Visual Studio Code", cwd],
                stdout=subprocess.DEVNULL,
                stderr=subprocess.DEVNULL,
                timeout=5,
            )
            return
        except Exception as exc:
            log(f"`open -a VS Code {cwd}` failed: {exc}")

    # Last resort: just activate VS Code via AppleScript.
    try:
        subprocess.run(
            ["osascript", "-e", 'tell application "Visual Studio Code" to activate'],
            stdout=subprocess.DEVNULL,
            stderr=subprocess.DEVNULL,
            timeout=5,
        )
    except Exception as exc:
        log(f"AppleScript activate failed: {exc}")


def _which(prog: str) -> bool:
    for p in os.environ.get("PATH", "").split(os.pathsep):
        candidate = os.path.join(p, prog)
        if os.path.isfile(candidate) and os.access(candidate, os.X_OK):
            return True
    return False


# --------------------------------------------------------------------------- #
# Background threads
# --------------------------------------------------------------------------- #
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
