vlgutv22/claude_mate/daemon/blelink.py

#!/usr/bin/env python3
"""BLE central for the Claude Mate device: the same line protocol, off the cable.

WHY THIS EXISTS
---------------
The Wi-Fi transport keeps an association open all day for a device that has
almost nothing to say. Status changes are rare and bursty -- a session goes
WAIT, forty minutes later it goes DONE -- and between them the radio is holding
a link up to transmit nothing. On a 14500 cell that is the wrong shape.

So the device advertises in short bursts (200 ms on, ~4 s off) instead, and this
module is the other half: a BLE central that finds it, connects, authenticates,
and then carries EXACTLY the bytes the serial and TCP links carry. No protocol
change. `F|`/`V|`/`M|`/`P` down, `H`/`K`/`B|` up, newline-delimited ASCII.

The duty-cycle figures come from issue #21, credited there to Jack Jansen in the
ESP8266/ESP32 group, who measured roughly 5% of normal consumption with that
rhythm on his own battery devices.

WHO IS THE CENTRAL
------------------
The Mac. Inverted from the TCP transport, where the device dials out, and for
the same reason in reverse: on BLE the low-power side should be the one that
advertises and sleeps between bursts, and the side with mains power and a real
scheduler should be the one doing the scanning. It also means the device needs
no address for the daemon at all -- no mDNS browse, no host field in the portal.

BLEAK IS OPTIONAL
-----------------
This module imports `bleak` at CALL time, not at import time, so a daemon
without it starts and runs exactly as before; `--ble` reports a clear message
instead of a traceback. The daemon's only hard third-party dependency stays
pyserial, which is a promise the README makes.
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
